trehansiddharth/SignAway/Logs/ADNS-9800 Diagram.png

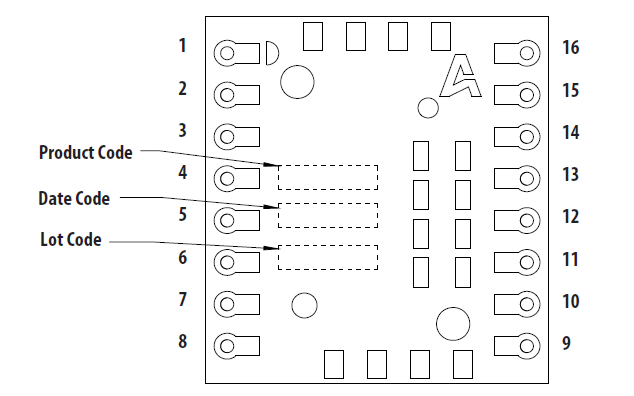
Logs/ADNS-9800 Diagram.png
