trehansiddharth/SignAway/Logs/Low NCS signal on 8051.png

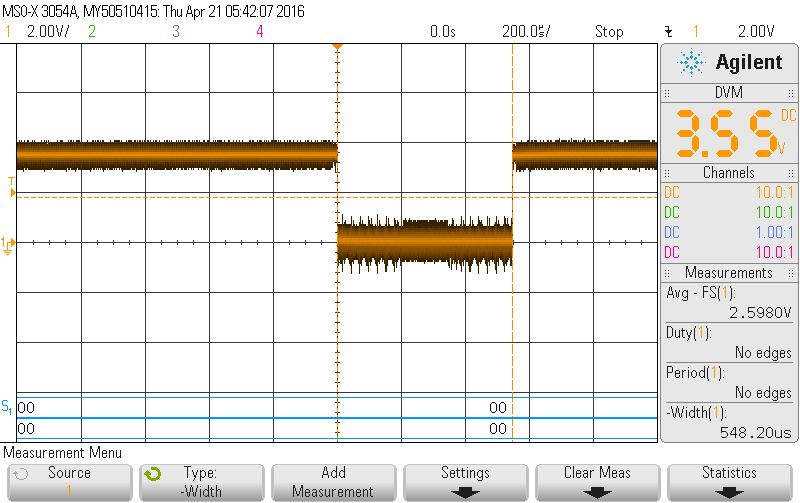
Logs/Low NCS signal on 8051.png
