trehansiddharth/SignAway/Logs/Reading MISO 1.png

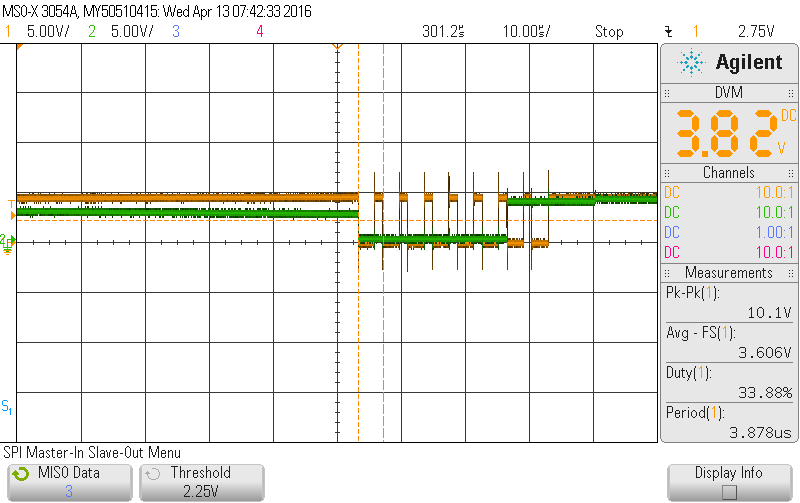
Logs/Reading MISO 1.png
