trehansiddharth/SignAway/Logs/Reading MISO 2.png

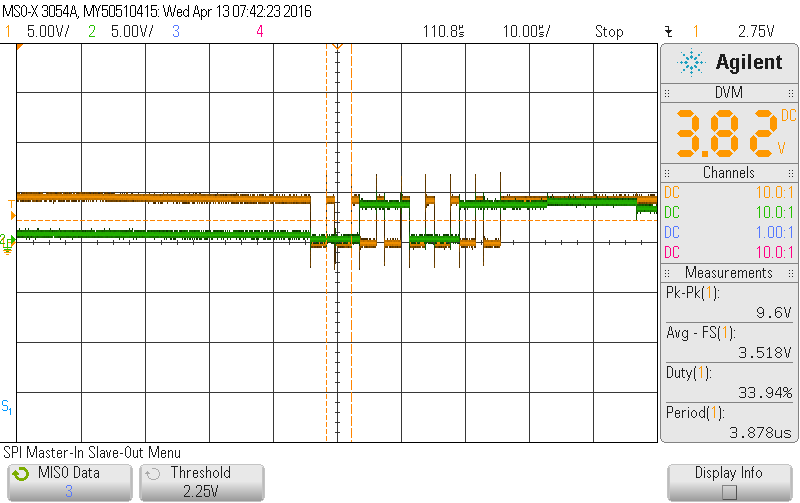
Logs/Reading MISO 2.png
