trehansiddharth/SignAway/Logs/SCLK and MOSI during write on 8051.png

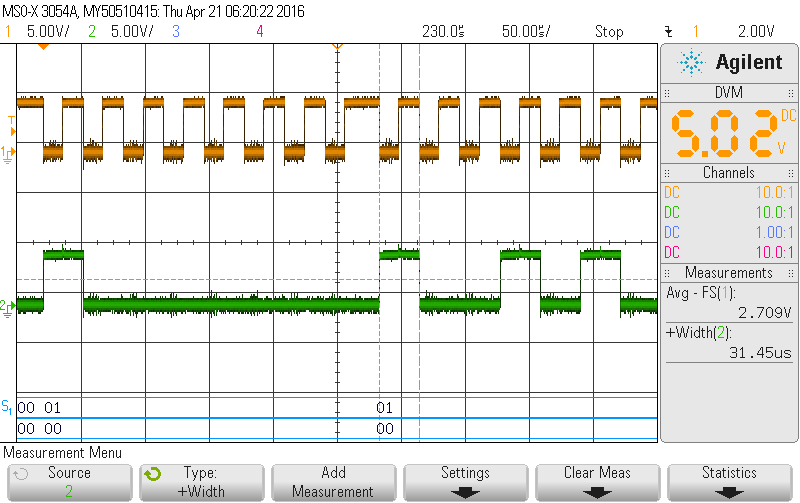
Logs/SCLK and MOSI during write on 8051.png
