trehansiddharth/SignAway/Logs/SCLK during read on 8051.png

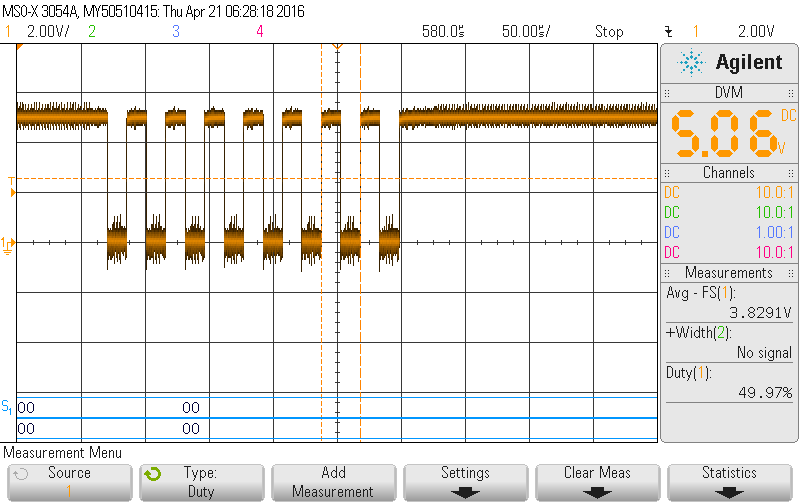
Logs/SCLK during read on 8051.png
