trehansiddharth/SignAway/Logs/SCLK during write on 8051.png

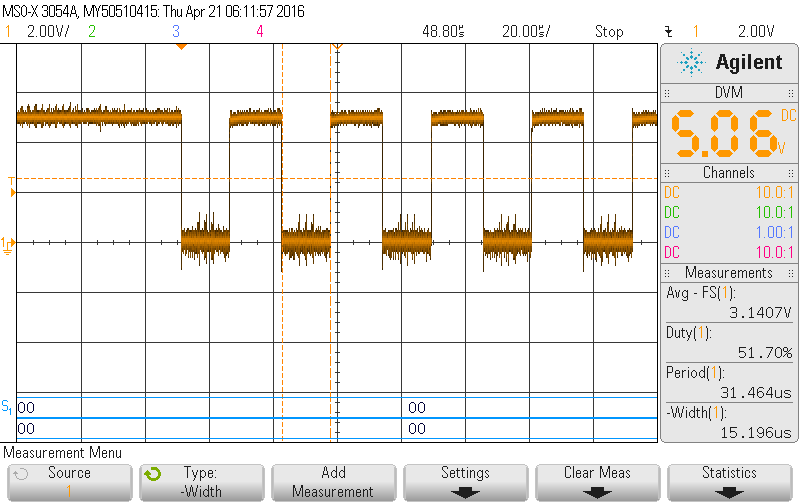
Logs/SCLK during write on 8051.png
