trehansiddharth/SignAway/Logs/Image Burst Operation Timing.png

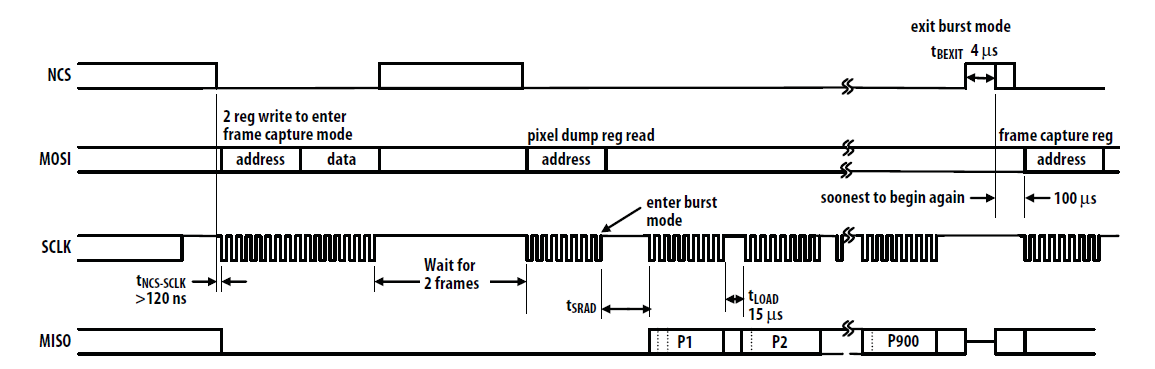
Logs/Image Burst Operation Timing.png
