trehansiddharth/SignAway/Logs/Read Operation Timing.png

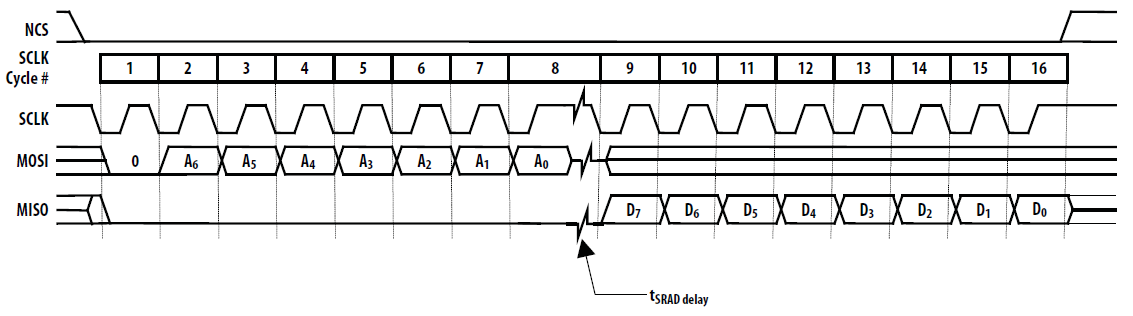
Logs/Read Operation Timing.png
