trehansiddharth/SignAway/Logs/Write Operation Timing.png

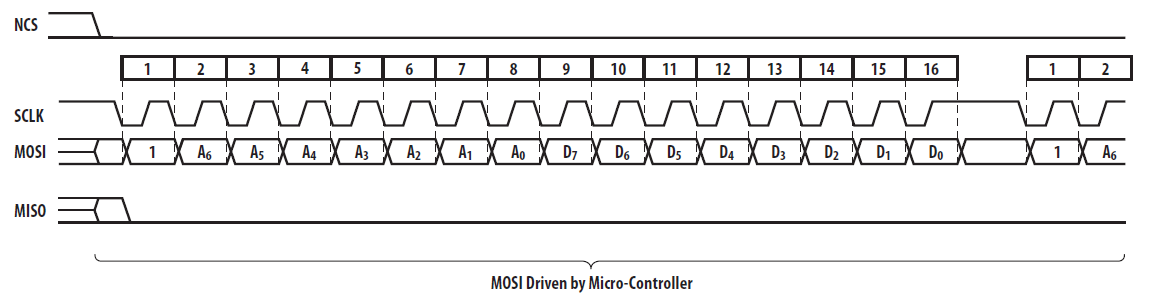
Logs/Write Operation Timing.png
