trehansiddharth/SignAway/Source/PSoC/SignatureVerifier/SignatureVerifier.cydsn/codegentemp/Pin_LED_Green.h

/*******************************************************************************
* File Name: Pin_LED_Green.h  
* Version 2.5
*
* Description:
*  This file containts Control Register function prototypes and register defines
*
* Note:
*
********************************************************************************
* Copyright 2008-2014, Cypress Semiconductor Corporation.  All rights reserved.
* You may use this file only in accordance with the license, terms, conditions, 
* disclaimers, and limitations in the end user license agreement accompanying 
* the software package with which this file was provided.
*******************************************************************************/

#if !defined(CY_PINS_Pin_LED_Green_H) /* Pins Pin_LED_Green_H */
#define CY_PINS_Pin_LED_Green_H

#include "cytypes.h"
#include "cyfitter.h"
#include "Pin_LED_Green_aliases.h"


/***************************************
*        Function Prototypes             
***************************************/    

void    Pin_LED_Green_Write(uint8 value) ;
void    Pin_LED_Green_SetDriveMode(uint8 mode) ;
uint8   Pin_LED_Green_ReadDataReg(void) ;
uint8   Pin_LED_Green_Read(void) ;
uint8   Pin_LED_Green_ClearInterrupt(void) ;


/***************************************
*           API Constants        
***************************************/

/* Drive Modes */
#define Pin_LED_Green_DRIVE_MODE_BITS        (3)
#define Pin_LED_Green_DRIVE_MODE_IND_MASK    (0xFFFFFFFFu >> (32 - Pin_LED_Green_DRIVE_MODE_BITS))
#define Pin_LED_Green_DRIVE_MODE_SHIFT       (0x00u)
#define Pin_LED_Green_DRIVE_MODE_MASK        (0x07u << Pin_LED_Green_DRIVE_MODE_SHIFT)

#define Pin_LED_Green_DM_ALG_HIZ         (0x00u << Pin_LED_Green_DRIVE_MODE_SHIFT)
#define Pin_LED_Green_DM_DIG_HIZ         (0x01u << Pin_LED_Green_DRIVE_MODE_SHIFT)
#define Pin_LED_Green_DM_RES_UP          (0x02u << Pin_LED_Green_DRIVE_MODE_SHIFT)
#define Pin_LED_Green_DM_RES_DWN         (0x03u << Pin_LED_Green_DRIVE_MODE_SHIFT)
#define Pin_LED_Green_DM_OD_LO           (0x04u << Pin_LED_Green_DRIVE_MODE_SHIFT)
#define Pin_LED_Green_DM_OD_HI           (0x05u << Pin_LED_Green_DRIVE_MODE_SHIFT)
#define Pin_LED_Green_DM_STRONG          (0x06u << Pin_LED_Green_DRIVE_MODE_SHIFT)
#define Pin_LED_Green_DM_RES_UPDWN       (0x07u << Pin_LED_Green_DRIVE_MODE_SHIFT)

/* Digital Port Constants */
#define Pin_LED_Green_MASK               Pin_LED_Green__MASK
#define Pin_LED_Green_SHIFT              Pin_LED_Green__SHIFT
#define Pin_LED_Green_WIDTH              1u


/***************************************
*             Registers        
***************************************/

/* Main Port Registers */
/* Pin State */
#define Pin_LED_Green_PS                     (* (reg32 *) Pin_LED_Green__PS)
/* Port Configuration */
#define Pin_LED_Green_PC                     (* (reg32 *) Pin_LED_Green__PC)
/* Data Register */
#define Pin_LED_Green_DR                     (* (reg32 *) Pin_LED_Green__DR)
/* Input Buffer Disable Override */
#define Pin_LED_Green_INP_DIS                (* (reg32 *) Pin_LED_Green__PC2)


#if defined(Pin_LED_Green__INTSTAT)  /* Interrupt Registers */

    #define Pin_LED_Green_INTSTAT                (* (reg32 *) Pin_LED_Green__INTSTAT)

#endif /* Interrupt Registers */

#endif /* End Pins Pin_LED_Green_H */


/* [] END OF FILE */
