trehansiddharth/SignAway/Source/PSoC/SignatureVerifier/SignatureVerifier.cydsn/codegentemp/Pin_SS.h

/*******************************************************************************
* File Name: Pin_SS.h  
* Version 2.5
*
* Description:
*  This file containts Control Register function prototypes and register defines
*
* Note:
*
********************************************************************************
* Copyright 2008-2014, Cypress Semiconductor Corporation.  All rights reserved.
* You may use this file only in accordance with the license, terms, conditions, 
* disclaimers, and limitations in the end user license agreement accompanying 
* the software package with which this file was provided.
*******************************************************************************/

#if !defined(CY_PINS_Pin_SS_H) /* Pins Pin_SS_H */
#define CY_PINS_Pin_SS_H

#include "cytypes.h"
#include "cyfitter.h"
#include "Pin_SS_aliases.h"


/***************************************
*        Function Prototypes             
***************************************/    

void    Pin_SS_Write(uint8 value) ;
void    Pin_SS_SetDriveMode(uint8 mode) ;
uint8   Pin_SS_ReadDataReg(void) ;
uint8   Pin_SS_Read(void) ;
uint8   Pin_SS_ClearInterrupt(void) ;


/***************************************
*           API Constants        
***************************************/

/* Drive Modes */
#define Pin_SS_DRIVE_MODE_BITS        (3)
#define Pin_SS_DRIVE_MODE_IND_MASK    (0xFFFFFFFFu >> (32 - Pin_SS_DRIVE_MODE_BITS))
#define Pin_SS_DRIVE_MODE_SHIFT       (0x00u)
#define Pin_SS_DRIVE_MODE_MASK        (0x07u << Pin_SS_DRIVE_MODE_SHIFT)

#define Pin_SS_DM_ALG_HIZ         (0x00u << Pin_SS_DRIVE_MODE_SHIFT)
#define Pin_SS_DM_DIG_HIZ         (0x01u << Pin_SS_DRIVE_MODE_SHIFT)
#define Pin_SS_DM_RES_UP          (0x02u << Pin_SS_DRIVE_MODE_SHIFT)
#define Pin_SS_DM_RES_DWN         (0x03u << Pin_SS_DRIVE_MODE_SHIFT)
#define Pin_SS_DM_OD_LO           (0x04u << Pin_SS_DRIVE_MODE_SHIFT)
#define Pin_SS_DM_OD_HI           (0x05u << Pin_SS_DRIVE_MODE_SHIFT)
#define Pin_SS_DM_STRONG          (0x06u << Pin_SS_DRIVE_MODE_SHIFT)
#define Pin_SS_DM_RES_UPDWN       (0x07u << Pin_SS_DRIVE_MODE_SHIFT)

/* Digital Port Constants */
#define Pin_SS_MASK               Pin_SS__MASK
#define Pin_SS_SHIFT              Pin_SS__SHIFT
#define Pin_SS_WIDTH              1u


/***************************************
*             Registers        
***************************************/

/* Main Port Registers */
/* Pin State */
#define Pin_SS_PS                     (* (reg32 *) Pin_SS__PS)
/* Port Configuration */
#define Pin_SS_PC                     (* (reg32 *) Pin_SS__PC)
/* Data Register */
#define Pin_SS_DR                     (* (reg32 *) Pin_SS__DR)
/* Input Buffer Disable Override */
#define Pin_SS_INP_DIS                (* (reg32 *) Pin_SS__PC2)


#if defined(Pin_SS__INTSTAT)  /* Interrupt Registers */

    #define Pin_SS_INTSTAT                (* (reg32 *) Pin_SS__INTSTAT)

#endif /* Interrupt Registers */

#endif /* End Pins Pin_SS_H */


/* [] END OF FILE */
