trehansiddharth/SignAway/Source/PSoC/SignatureVerifier/SignatureVerifier.cydsn/codegentemp/cyfitter.h

#ifndef INCLUDED_CYFITTER_H
#define INCLUDED_CYFITTER_H
#include <cydevice_trm.h>

/* SPI_BSPIS */
#define SPI_BSPIS_es3_SPISlave_BitCounter__16BIT_CONTROL_AUX_CTL_REG CYREG_UDB_W16_ACTL_02
#define SPI_BSPIS_es3_SPISlave_BitCounter__16BIT_CONTROL_CONTROL_REG CYREG_UDB_W16_CTL_02
#define SPI_BSPIS_es3_SPISlave_BitCounter__16BIT_CONTROL_COUNT_REG CYREG_UDB_W16_CTL_02
#define SPI_BSPIS_es3_SPISlave_BitCounter__16BIT_COUNT_CONTROL_REG CYREG_UDB_W16_CTL_02
#define SPI_BSPIS_es3_SPISlave_BitCounter__16BIT_COUNT_COUNT_REG CYREG_UDB_W16_CTL_02
#define SPI_BSPIS_es3_SPISlave_BitCounter__16BIT_MASK_MASK_REG CYREG_UDB_W16_MSK_02
#define SPI_BSPIS_es3_SPISlave_BitCounter__16BIT_MASK_PERIOD_REG CYREG_UDB_W16_MSK_02
#define SPI_BSPIS_es3_SPISlave_BitCounter__16BIT_PERIOD_MASK_REG CYREG_UDB_W16_MSK_02
#define SPI_BSPIS_es3_SPISlave_BitCounter__16BIT_PERIOD_PERIOD_REG CYREG_UDB_W16_MSK_02
#define SPI_BSPIS_es3_SPISlave_BitCounter__CONTROL_AUX_CTL_REG CYREG_UDB_W8_ACTL_02
#define SPI_BSPIS_es3_SPISlave_BitCounter__CONTROL_REG CYREG_UDB_W8_CTL_02
#define SPI_BSPIS_es3_SPISlave_BitCounter__CONTROL_ST_REG CYREG_UDB_CAT16_CTL_ST_02
#define SPI_BSPIS_es3_SPISlave_BitCounter__COUNT_REG CYREG_UDB_W8_CTL_02
#define SPI_BSPIS_es3_SPISlave_BitCounter__COUNT_ST_REG CYREG_UDB_CAT16_CTL_ST_02
#define SPI_BSPIS_es3_SPISlave_BitCounter__MASK_CTL_AUX_CTL_REG CYREG_UDB_CAT16_ACTL_MSK_02
#define SPI_BSPIS_es3_SPISlave_BitCounter__PER_CTL_AUX_CTL_REG CYREG_UDB_CAT16_ACTL_MSK_02
#define SPI_BSPIS_es3_SPISlave_BitCounter__PERIOD_REG CYREG_UDB_W8_MSK_02
#define SPI_BSPIS_es3_SPISlave_BitCounter_ST__16BIT_STATUS_AUX_CTL_REG CYREG_UDB_W16_ACTL_02
#define SPI_BSPIS_es3_SPISlave_BitCounter_ST__16BIT_STATUS_REG CYREG_UDB_W16_ST_02
#define SPI_BSPIS_es3_SPISlave_BitCounter_ST__MASK_REG CYREG_UDB_W8_MSK_02
#define SPI_BSPIS_es3_SPISlave_BitCounter_ST__MASK_ST_AUX_CTL_REG CYREG_UDB_CAT16_ACTL_MSK_02
#define SPI_BSPIS_es3_SPISlave_BitCounter_ST__PER_ST_AUX_CTL_REG CYREG_UDB_CAT16_ACTL_MSK_02
#define SPI_BSPIS_es3_SPISlave_BitCounter_ST__STATUS_AUX_CTL_REG CYREG_UDB_W8_ACTL_02
#define SPI_BSPIS_es3_SPISlave_BitCounter_ST__STATUS_CNT_REG CYREG_UDB_CAT16_CTL_ST_02
#define SPI_BSPIS_es3_SPISlave_BitCounter_ST__STATUS_CONTROL_REG CYREG_UDB_CAT16_CTL_ST_02
#define SPI_BSPIS_es3_SPISlave_BitCounter_ST__STATUS_REG CYREG_UDB_W8_ST_02
#define SPI_BSPIS_es3_SPISlave_RxStsReg__16BIT_STATUS_AUX_CTL_REG CYREG_UDB_W16_ACTL_01
#define SPI_BSPIS_es3_SPISlave_RxStsReg__16BIT_STATUS_REG CYREG_UDB_W16_ST_01
#define SPI_BSPIS_es3_SPISlave_RxStsReg__3__MASK 0x08u
#define SPI_BSPIS_es3_SPISlave_RxStsReg__3__POS 3
#define SPI_BSPIS_es3_SPISlave_RxStsReg__4__MASK 0x10u
#define SPI_BSPIS_es3_SPISlave_RxStsReg__4__POS 4
#define SPI_BSPIS_es3_SPISlave_RxStsReg__5__MASK 0x20u
#define SPI_BSPIS_es3_SPISlave_RxStsReg__5__POS 5
#define SPI_BSPIS_es3_SPISlave_RxStsReg__6__MASK 0x40u
#define SPI_BSPIS_es3_SPISlave_RxStsReg__6__POS 6
#define SPI_BSPIS_es3_SPISlave_RxStsReg__MASK 0x78u
#define SPI_BSPIS_es3_SPISlave_RxStsReg__MASK_REG CYREG_UDB_W8_MSK_01
#define SPI_BSPIS_es3_SPISlave_RxStsReg__STATUS_AUX_CTL_REG CYREG_UDB_W8_ACTL_01
#define SPI_BSPIS_es3_SPISlave_RxStsReg__STATUS_REG CYREG_UDB_W8_ST_01
#define SPI_BSPIS_es3_SPISlave_sR16_Dp_u0__16BIT_A0_REG CYREG_UDB_W16_A0_02
#define SPI_BSPIS_es3_SPISlave_sR16_Dp_u0__16BIT_A1_REG CYREG_UDB_W16_A1_02
#define SPI_BSPIS_es3_SPISlave_sR16_Dp_u0__16BIT_D0_REG CYREG_UDB_W16_D0_02
#define SPI_BSPIS_es3_SPISlave_sR16_Dp_u0__16BIT_D1_REG CYREG_UDB_W16_D1_02
#define SPI_BSPIS_es3_SPISlave_sR16_Dp_u0__16BIT_DP_AUX_CTL_REG CYREG_UDB_W16_ACTL_02
#define SPI_BSPIS_es3_SPISlave_sR16_Dp_u0__16BIT_F0_REG CYREG_UDB_W16_F0_02
#define SPI_BSPIS_es3_SPISlave_sR16_Dp_u0__16BIT_F1_REG CYREG_UDB_W16_F1_02
#define SPI_BSPIS_es3_SPISlave_sR16_Dp_u0__A0_A1_REG CYREG_UDB_CAT16_A_02
#define SPI_BSPIS_es3_SPISlave_sR16_Dp_u0__A0_REG CYREG_UDB_W8_A0_02
#define SPI_BSPIS_es3_SPISlave_sR16_Dp_u0__A1_REG CYREG_UDB_W8_A1_02
#define SPI_BSPIS_es3_SPISlave_sR16_Dp_u0__D0_D1_REG CYREG_UDB_CAT16_D_02
#define SPI_BSPIS_es3_SPISlave_sR16_Dp_u0__D0_REG CYREG_UDB_W8_D0_02
#define SPI_BSPIS_es3_SPISlave_sR16_Dp_u0__D1_REG CYREG_UDB_W8_D1_02
#define SPI_BSPIS_es3_SPISlave_sR16_Dp_u0__DP_AUX_CTL_REG CYREG_UDB_W8_ACTL_02
#define SPI_BSPIS_es3_SPISlave_sR16_Dp_u0__F0_F1_REG CYREG_UDB_CAT16_F_02
#define SPI_BSPIS_es3_SPISlave_sR16_Dp_u0__F0_REG CYREG_UDB_W8_F0_02
#define SPI_BSPIS_es3_SPISlave_sR16_Dp_u0__F1_REG CYREG_UDB_W8_F1_02
#define SPI_BSPIS_es3_SPISlave_sR16_Dp_u0__MSK_DP_AUX_CTL_REG CYREG_UDB_CAT16_ACTL_MSK_02
#define SPI_BSPIS_es3_SPISlave_sR16_Dp_u0__PER_DP_AUX_CTL_REG CYREG_UDB_CAT16_ACTL_MSK_02
#define SPI_BSPIS_es3_SPISlave_sR16_Dp_u1__A0_A1_REG CYREG_UDB_CAT16_A_03
#define SPI_BSPIS_es3_SPISlave_sR16_Dp_u1__A0_REG CYREG_UDB_W8_A0_03
#define SPI_BSPIS_es3_SPISlave_sR16_Dp_u1__A1_REG CYREG_UDB_W8_A1_03
#define SPI_BSPIS_es3_SPISlave_sR16_Dp_u1__D0_D1_REG CYREG_UDB_CAT16_D_03
#define SPI_BSPIS_es3_SPISlave_sR16_Dp_u1__D0_REG CYREG_UDB_W8_D0_03
#define SPI_BSPIS_es3_SPISlave_sR16_Dp_u1__D1_REG CYREG_UDB_W8_D1_03
#define SPI_BSPIS_es3_SPISlave_sR16_Dp_u1__DP_AUX_CTL_REG CYREG_UDB_W8_ACTL_03
#define SPI_BSPIS_es3_SPISlave_sR16_Dp_u1__F0_F1_REG CYREG_UDB_CAT16_F_03
#define SPI_BSPIS_es3_SPISlave_sR16_Dp_u1__F0_REG CYREG_UDB_W8_F0_03
#define SPI_BSPIS_es3_SPISlave_sR16_Dp_u1__F1_REG CYREG_UDB_W8_F1_03
#define SPI_BSPIS_es3_SPISlave_TxStsReg__0__MASK 0x01u
#define SPI_BSPIS_es3_SPISlave_TxStsReg__0__POS 0
#define SPI_BSPIS_es3_SPISlave_TxStsReg__1__MASK 0x02u
#define SPI_BSPIS_es3_SPISlave_TxStsReg__1__POS 1
#define SPI_BSPIS_es3_SPISlave_TxStsReg__2__MASK 0x04u
#define SPI_BSPIS_es3_SPISlave_TxStsReg__2__POS 2
#define SPI_BSPIS_es3_SPISlave_TxStsReg__6__MASK 0x40u
#define SPI_BSPIS_es3_SPISlave_TxStsReg__6__POS 6
#define SPI_BSPIS_es3_SPISlave_TxStsReg__MASK 0x47u
#define SPI_BSPIS_es3_SPISlave_TxStsReg__MASK_REG CYREG_UDB_W8_MSK_03
#define SPI_BSPIS_es3_SPISlave_TxStsReg__STATUS_AUX_CTL_REG CYREG_UDB_W8_ACTL_03
#define SPI_BSPIS_es3_SPISlave_TxStsReg__STATUS_REG CYREG_UDB_W8_ST_03

/* SPI_Clock */
#define SPI_Clock__DIVIDER_MASK 0x0000FFFFu
#define SPI_Clock__ENABLE CYREG_CLK_DIVIDER_A00
#define SPI_Clock__ENABLE_MASK 0x80000000u
#define SPI_Clock__MASK 0x80000000u
#define SPI_Clock__REGISTER CYREG_CLK_DIVIDER_A00

/* SPI_RxInternalInterrupt */
#define SPI_RxInternalInterrupt__INTC_CLR_EN_REG CYREG_CM0_ICER
#define SPI_RxInternalInterrupt__INTC_CLR_PD_REG CYREG_CM0_ICPR
#define SPI_RxInternalInterrupt__INTC_MASK 0x01u
#define SPI_RxInternalInterrupt__INTC_NUMBER 0u
#define SPI_RxInternalInterrupt__INTC_PRIOR_MASK 0xC0u
#define SPI_RxInternalInterrupt__INTC_PRIOR_NUM 3u
#define SPI_RxInternalInterrupt__INTC_PRIOR_REG CYREG_CM0_IPR0
#define SPI_RxInternalInterrupt__INTC_SET_EN_REG CYREG_CM0_ISER
#define SPI_RxInternalInterrupt__INTC_SET_PD_REG CYREG_CM0_ISPR

/* UART_rx */
#define UART_rx__0__DM__MASK 0x07u
#define UART_rx__0__DM__SHIFT 0
#define UART_rx__0__DR CYREG_PRT3_DR
#define UART_rx__0__HSIOM CYREG_HSIOM_PORT_SEL3
#define UART_rx__0__HSIOM_MASK 0x0000000Fu
#define UART_rx__0__HSIOM_SHIFT 0u
#define UART_rx__0__INTCFG CYREG_PRT3_INTCFG
#define UART_rx__0__INTSTAT CYREG_PRT3_INTSTAT
#define UART_rx__0__MASK 0x01u
#define UART_rx__0__PA__CFG0 CYREG_UDB_PA3_CFG0
#define UART_rx__0__PA__CFG1 CYREG_UDB_PA3_CFG1
#define UART_rx__0__PA__CFG10 CYREG_UDB_PA3_CFG10
#define UART_rx__0__PA__CFG11 CYREG_UDB_PA3_CFG11
#define UART_rx__0__PA__CFG12 CYREG_UDB_PA3_CFG12
#define UART_rx__0__PA__CFG13 CYREG_UDB_PA3_CFG13
#define UART_rx__0__PA__CFG14 CYREG_UDB_PA3_CFG14
#define UART_rx__0__PA__CFG2 CYREG_UDB_PA3_CFG2
#define UART_rx__0__PA__CFG3 CYREG_UDB_PA3_CFG3
#define UART_rx__0__PA__CFG4 CYREG_UDB_PA3_CFG4
#define UART_rx__0__PA__CFG5 CYREG_UDB_PA3_CFG5
#define UART_rx__0__PA__CFG6 CYREG_UDB_PA3_CFG6
#define UART_rx__0__PA__CFG7 CYREG_UDB_PA3_CFG7
#define UART_rx__0__PA__CFG8 CYREG_UDB_PA3_CFG8
#define UART_rx__0__PA__CFG9 CYREG_UDB_PA3_CFG9
#define UART_rx__0__PC CYREG_PRT3_PC
#define UART_rx__0__PC2 CYREG_PRT3_PC2
#define UART_rx__0__PORT 3u
#define UART_rx__0__PS CYREG_PRT3_PS
#define UART_rx__0__SHIFT 0
#define UART_rx__DR CYREG_PRT3_DR
#define UART_rx__INTCFG CYREG_PRT3_INTCFG
#define UART_rx__INTSTAT CYREG_PRT3_INTSTAT
#define UART_rx__MASK 0x01u
#define UART_rx__PA__CFG0 CYREG_UDB_PA3_CFG0
#define UART_rx__PA__CFG1 CYREG_UDB_PA3_CFG1
#define UART_rx__PA__CFG10 CYREG_UDB_PA3_CFG10
#define UART_rx__PA__CFG11 CYREG_UDB_PA3_CFG11
#define UART_rx__PA__CFG12 CYREG_UDB_PA3_CFG12
#define UART_rx__PA__CFG13 CYREG_UDB_PA3_CFG13
#define UART_rx__PA__CFG14 CYREG_UDB_PA3_CFG14
#define UART_rx__PA__CFG2 CYREG_UDB_PA3_CFG2
#define UART_rx__PA__CFG3 CYREG_UDB_PA3_CFG3
#define UART_rx__PA__CFG4 CYREG_UDB_PA3_CFG4
#define UART_rx__PA__CFG5 CYREG_UDB_PA3_CFG5
#define UART_rx__PA__CFG6 CYREG_UDB_PA3_CFG6
#define UART_rx__PA__CFG7 CYREG_UDB_PA3_CFG7
#define UART_rx__PA__CFG8 CYREG_UDB_PA3_CFG8
#define UART_rx__PA__CFG9 CYREG_UDB_PA3_CFG9
#define UART_rx__PC CYREG_PRT3_PC
#define UART_rx__PC2 CYREG_PRT3_PC2
#define UART_rx__PORT 3u
#define UART_rx__PS CYREG_PRT3_PS
#define UART_rx__SHIFT 0

/* UART_SCB */
#define UART_SCB__BIST_CONTROL CYREG_SCB1_BIST_CONTROL
#define UART_SCB__BIST_DATA CYREG_SCB1_BIST_DATA
#define UART_SCB__CTRL CYREG_SCB1_CTRL
#define UART_SCB__EZ_DATA00 CYREG_SCB1_EZ_DATA00
#define UART_SCB__EZ_DATA01 CYREG_SCB1_EZ_DATA01
#define UART_SCB__EZ_DATA02 CYREG_SCB1_EZ_DATA02
#define UART_SCB__EZ_DATA03 CYREG_SCB1_EZ_DATA03
#define UART_SCB__EZ_DATA04 CYREG_SCB1_EZ_DATA04
#define UART_SCB__EZ_DATA05 CYREG_SCB1_EZ_DATA05
#define UART_SCB__EZ_DATA06 CYREG_SCB1_EZ_DATA06
#define UART_SCB__EZ_DATA07 CYREG_SCB1_EZ_DATA07
#define UART_SCB__EZ_DATA08 CYREG_SCB1_EZ_DATA08
#define UART_SCB__EZ_DATA09 CYREG_SCB1_EZ_DATA09
#define UART_SCB__EZ_DATA10 CYREG_SCB1_EZ_DATA10
#define UART_SCB__EZ_DATA11 CYREG_SCB1_EZ_DATA11
#define UART_SCB__EZ_DATA12 CYREG_SCB1_EZ_DATA12
#define UART_SCB__EZ_DATA13 CYREG_SCB1_EZ_DATA13
#define UART_SCB__EZ_DATA14 CYREG_SCB1_EZ_DATA14
#define UART_SCB__EZ_DATA15 CYREG_SCB1_EZ_DATA15
#define UART_SCB__EZ_DATA16 CYREG_SCB1_EZ_DATA16
#define UART_SCB__EZ_DATA17 CYREG_SCB1_EZ_DATA17
#define UART_SCB__EZ_DATA18 CYREG_SCB1_EZ_DATA18
#define UART_SCB__EZ_DATA19 CYREG_SCB1_EZ_DATA19
#define UART_SCB__EZ_DATA20 CYREG_SCB1_EZ_DATA20
#define UART_SCB__EZ_DATA21 CYREG_SCB1_EZ_DATA21
#define UART_SCB__EZ_DATA22 CYREG_SCB1_EZ_DATA22
#define UART_SCB__EZ_DATA23 CYREG_SCB1_EZ_DATA23
#define UART_SCB__EZ_DATA24 CYREG_SCB1_EZ_DATA24
#define UART_SCB__EZ_DATA25 CYREG_SCB1_EZ_DATA25
#define UART_SCB__EZ_DATA26 CYREG_SCB1_EZ_DATA26
#define UART_SCB__EZ_DATA27 CYREG_SCB1_EZ_DATA27
#define UART_SCB__EZ_DATA28 CYREG_SCB1_EZ_DATA28
#define UART_SCB__EZ_DATA29 CYREG_SCB1_EZ_DATA29
#define UART_SCB__EZ_DATA30 CYREG_SCB1_EZ_DATA30
#define UART_SCB__EZ_DATA31 CYREG_SCB1_EZ_DATA31
#define UART_SCB__I2C_CFG CYREG_SCB1_I2C_CFG
#define UART_SCB__I2C_CTRL CYREG_SCB1_I2C_CTRL
#define UART_SCB__I2C_M_CMD CYREG_SCB1_I2C_M_CMD
#define UART_SCB__I2C_S_CMD CYREG_SCB1_I2C_S_CMD
#define UART_SCB__I2C_STATUS CYREG_SCB1_I2C_STATUS
#define UART_SCB__INTR_CAUSE CYREG_SCB1_INTR_CAUSE
#define UART_SCB__INTR_I2C_EC CYREG_SCB1_INTR_I2C_EC
#define UART_SCB__INTR_I2C_EC_MASK CYREG_SCB1_INTR_I2C_EC_MASK
#define UART_SCB__INTR_I2C_EC_MASKED CYREG_SCB1_INTR_I2C_EC_MASKED
#define UART_SCB__INTR_M CYREG_SCB1_INTR_M
#define UART_SCB__INTR_M_MASK CYREG_SCB1_INTR_M_MASK
#define UART_SCB__INTR_M_MASKED CYREG_SCB1_INTR_M_MASKED
#define UART_SCB__INTR_M_SET CYREG_SCB1_INTR_M_SET
#define UART_SCB__INTR_RX CYREG_SCB1_INTR_RX
#define UART_SCB__INTR_RX_MASK CYREG_SCB1_INTR_RX_MASK
#define UART_SCB__INTR_RX_MASKED CYREG_SCB1_INTR_RX_MASKED
#define UART_SCB__INTR_RX_SET CYREG_SCB1_INTR_RX_SET
#define UART_SCB__INTR_S CYREG_SCB1_INTR_S
#define UART_SCB__INTR_S_MASK CYREG_SCB1_INTR_S_MASK
#define UART_SCB__INTR_S_MASKED CYREG_SCB1_INTR_S_MASKED
#define UART_SCB__INTR_S_SET CYREG_SCB1_INTR_S_SET
#define UART_SCB__INTR_SPI_EC CYREG_SCB1_INTR_SPI_EC
#define UART_SCB__INTR_SPI_EC_MASK CYREG_SCB1_INTR_SPI_EC_MASK
#define UART_SCB__INTR_SPI_EC_MASKED CYREG_SCB1_INTR_SPI_EC_MASKED
#define UART_SCB__INTR_TX CYREG_SCB1_INTR_TX
#define UART_SCB__INTR_TX_MASK CYREG_SCB1_INTR_TX_MASK
#define UART_SCB__INTR_TX_MASKED CYREG_SCB1_INTR_TX_MASKED
#define UART_SCB__INTR_TX_SET CYREG_SCB1_INTR_TX_SET
#define UART_SCB__RX_CTRL CYREG_SCB1_RX_CTRL
#define UART_SCB__RX_FIFO_CTRL CYREG_SCB1_RX_FIFO_CTRL
#define UART_SCB__RX_FIFO_RD CYREG_SCB1_RX_FIFO_RD
#define UART_SCB__RX_FIFO_RD_SILENT CYREG_SCB1_RX_FIFO_RD_SILENT
#define UART_SCB__RX_FIFO_STATUS CYREG_SCB1_RX_FIFO_STATUS
#define UART_SCB__RX_MATCH CYREG_SCB1_RX_MATCH
#define UART_SCB__SPI_CTRL CYREG_SCB1_SPI_CTRL
#define UART_SCB__SPI_STATUS CYREG_SCB1_SPI_STATUS
#define UART_SCB__STATUS CYREG_SCB1_STATUS
#define UART_SCB__TX_CTRL CYREG_SCB1_TX_CTRL
#define UART_SCB__TX_FIFO_CTRL CYREG_SCB1_TX_FIFO_CTRL
#define UART_SCB__TX_FIFO_STATUS CYREG_SCB1_TX_FIFO_STATUS
#define UART_SCB__TX_FIFO_WR CYREG_SCB1_TX_FIFO_WR
#define UART_SCB__UART_CTRL CYREG_SCB1_UART_CTRL
#define UART_SCB__UART_RX_CTRL CYREG_SCB1_UART_RX_CTRL
#define UART_SCB__UART_RX_STATUS CYREG_SCB1_UART_RX_STATUS
#define UART_SCB__UART_TX_CTRL CYREG_SCB1_UART_TX_CTRL

/* UART_SCBCLK */
#define UART_SCBCLK__DIVIDER_MASK 0x0000FFFFu
#define UART_SCBCLK__ENABLE CYREG_CLK_DIVIDER_B00
#define UART_SCBCLK__ENABLE_MASK 0x80000000u
#define UART_SCBCLK__MASK 0x80000000u
#define UART_SCBCLK__REGISTER CYREG_CLK_DIVIDER_B00

/* UART_tx */
#define UART_tx__0__DM__MASK 0x38u
#define UART_tx__0__DM__SHIFT 3
#define UART_tx__0__DR CYREG_PRT3_DR
#define UART_tx__0__HSIOM CYREG_HSIOM_PORT_SEL3
#define UART_tx__0__HSIOM_MASK 0x000000F0u
#define UART_tx__0__HSIOM_SHIFT 4u
#define UART_tx__0__INTCFG CYREG_PRT3_INTCFG
#define UART_tx__0__INTSTAT CYREG_PRT3_INTSTAT
#define UART_tx__0__MASK 0x02u
#define UART_tx__0__OUT_SEL CYREG_UDB_PA3_CFG10
#define UART_tx__0__OUT_SEL_SHIFT 2u
#define UART_tx__0__OUT_SEL_VAL -1u
#define UART_tx__0__PA__CFG0 CYREG_UDB_PA3_CFG0
#define UART_tx__0__PA__CFG1 CYREG_UDB_PA3_CFG1
#define UART_tx__0__PA__CFG10 CYREG_UDB_PA3_CFG10
#define UART_tx__0__PA__CFG11 CYREG_UDB_PA3_CFG11
#define UART_tx__0__PA__CFG12 CYREG_UDB_PA3_CFG12
#define UART_tx__0__PA__CFG13 CYREG_UDB_PA3_CFG13
#define UART_tx__0__PA__CFG14 CYREG_UDB_PA3_CFG14
#define UART_tx__0__PA__CFG2 CYREG_UDB_PA3_CFG2
#define UART_tx__0__PA__CFG3 CYREG_UDB_PA3_CFG3
#define UART_tx__0__PA__CFG4 CYREG_UDB_PA3_CFG4
#define UART_tx__0__PA__CFG5 CYREG_UDB_PA3_CFG5
#define UART_tx__0__PA__CFG6 CYREG_UDB_PA3_CFG6
#define UART_tx__0__PA__CFG7 CYREG_UDB_PA3_CFG7
#define UART_tx__0__PA__CFG8 CYREG_UDB_PA3_CFG8
#define UART_tx__0__PA__CFG9 CYREG_UDB_PA3_CFG9
#define UART_tx__0__PC CYREG_PRT3_PC
#define UART_tx__0__PC2 CYREG_PRT3_PC2
#define UART_tx__0__PORT 3u
#define UART_tx__0__PS CYREG_PRT3_PS
#define UART_tx__0__SHIFT 1
#define UART_tx__DR CYREG_PRT3_DR
#define UART_tx__INTCFG CYREG_PRT3_INTCFG
#define UART_tx__INTSTAT CYREG_PRT3_INTSTAT
#define UART_tx__MASK 0x02u
#define UART_tx__PA__CFG0 CYREG_UDB_PA3_CFG0
#define UART_tx__PA__CFG1 CYREG_UDB_PA3_CFG1
#define UART_tx__PA__CFG10 CYREG_UDB_PA3_CFG10
#define UART_tx__PA__CFG11 CYREG_UDB_PA3_CFG11
#define UART_tx__PA__CFG12 CYREG_UDB_PA3_CFG12
#define UART_tx__PA__CFG13 CYREG_UDB_PA3_CFG13
#define UART_tx__PA__CFG14 CYREG_UDB_PA3_CFG14
#define UART_tx__PA__CFG2 CYREG_UDB_PA3_CFG2
#define UART_tx__PA__CFG3 CYREG_UDB_PA3_CFG3
#define UART_tx__PA__CFG4 CYREG_UDB_PA3_CFG4
#define UART_tx__PA__CFG5 CYREG_UDB_PA3_CFG5
#define UART_tx__PA__CFG6 CYREG_UDB_PA3_CFG6
#define UART_tx__PA__CFG7 CYREG_UDB_PA3_CFG7
#define UART_tx__PA__CFG8 CYREG_UDB_PA3_CFG8
#define UART_tx__PA__CFG9 CYREG_UDB_PA3_CFG9
#define UART_tx__PC CYREG_PRT3_PC
#define UART_tx__PC2 CYREG_PRT3_PC2
#define UART_tx__PORT 3u
#define UART_tx__PS CYREG_PRT3_PS
#define UART_tx__SHIFT 1

/* Pin_SS */
#define Pin_SS__0__DM__MASK 0x1C0u
#define Pin_SS__0__DM__SHIFT 6
#define Pin_SS__0__DR CYREG_PRT0_DR
#define Pin_SS__0__HSIOM CYREG_HSIOM_PORT_SEL0
#define Pin_SS__0__HSIOM_MASK 0x00000F00u
#define Pin_SS__0__HSIOM_SHIFT 8u
#define Pin_SS__0__INTCFG CYREG_PRT0_INTCFG
#define Pin_SS__0__INTSTAT CYREG_PRT0_INTSTAT
#define Pin_SS__0__MASK 0x04u
#define Pin_SS__0__PA__CFG0 CYREG_UDB_PA0_CFG0
#define Pin_SS__0__PA__CFG1 CYREG_UDB_PA0_CFG1
#define Pin_SS__0__PA__CFG10 CYREG_UDB_PA0_CFG10
#define Pin_SS__0__PA__CFG11 CYREG_UDB_PA0_CFG11
#define Pin_SS__0__PA__CFG12 CYREG_UDB_PA0_CFG12
#define Pin_SS__0__PA__CFG13 CYREG_UDB_PA0_CFG13
#define Pin_SS__0__PA__CFG14 CYREG_UDB_PA0_CFG14
#define Pin_SS__0__PA__CFG2 CYREG_UDB_PA0_CFG2
#define Pin_SS__0__PA__CFG3 CYREG_UDB_PA0_CFG3
#define Pin_SS__0__PA__CFG4 CYREG_UDB_PA0_CFG4
#define Pin_SS__0__PA__CFG5 CYREG_UDB_PA0_CFG5
#define Pin_SS__0__PA__CFG6 CYREG_UDB_PA0_CFG6
#define Pin_SS__0__PA__CFG7 CYREG_UDB_PA0_CFG7
#define Pin_SS__0__PA__CFG8 CYREG_UDB_PA0_CFG8
#define Pin_SS__0__PA__CFG9 CYREG_UDB_PA0_CFG9
#define Pin_SS__0__PC CYREG_PRT0_PC
#define Pin_SS__0__PC2 CYREG_PRT0_PC2
#define Pin_SS__0__PORT 0u
#define Pin_SS__0__PS CYREG_PRT0_PS
#define Pin_SS__0__SHIFT 2
#define Pin_SS__DR CYREG_PRT0_DR
#define Pin_SS__INTCFG CYREG_PRT0_INTCFG
#define Pin_SS__INTSTAT CYREG_PRT0_INTSTAT
#define Pin_SS__MASK 0x04u
#define Pin_SS__PA__CFG0 CYREG_UDB_PA0_CFG0
#define Pin_SS__PA__CFG1 CYREG_UDB_PA0_CFG1
#define Pin_SS__PA__CFG10 CYREG_UDB_PA0_CFG10
#define Pin_SS__PA__CFG11 CYREG_UDB_PA0_CFG11
#define Pin_SS__PA__CFG12 CYREG_UDB_PA0_CFG12
#define Pin_SS__PA__CFG13 CYREG_UDB_PA0_CFG13
#define Pin_SS__PA__CFG14 CYREG_UDB_PA0_CFG14
#define Pin_SS__PA__CFG2 CYREG_UDB_PA0_CFG2
#define Pin_SS__PA__CFG3 CYREG_UDB_PA0_CFG3
#define Pin_SS__PA__CFG4 CYREG_UDB_PA0_CFG4
#define Pin_SS__PA__CFG5 CYREG_UDB_PA0_CFG5
#define Pin_SS__PA__CFG6 CYREG_UDB_PA0_CFG6
#define Pin_SS__PA__CFG7 CYREG_UDB_PA0_CFG7
#define Pin_SS__PA__CFG8 CYREG_UDB_PA0_CFG8
#define Pin_SS__PA__CFG9 CYREG_UDB_PA0_CFG9
#define Pin_SS__PC CYREG_PRT0_PC
#define Pin_SS__PC2 CYREG_PRT0_PC2
#define Pin_SS__PORT 0u
#define Pin_SS__PS CYREG_PRT0_PS
#define Pin_SS__SHIFT 2

/* isr_spi */
#define isr_spi__INTC_CLR_EN_REG CYREG_CM0_ICER
#define isr_spi__INTC_CLR_PD_REG CYREG_CM0_ICPR
#define isr_spi__INTC_MASK 0x02u
#define isr_spi__INTC_NUMBER 1u
#define isr_spi__INTC_PRIOR_MASK 0xC000u
#define isr_spi__INTC_PRIOR_NUM 3u
#define isr_spi__INTC_PRIOR_REG CYREG_CM0_IPR0
#define isr_spi__INTC_SET_EN_REG CYREG_CM0_ISER
#define isr_spi__INTC_SET_PD_REG CYREG_CM0_ISPR

/* Pin_MOSI */
#define Pin_MOSI__0__DM__MASK 0x07u
#define Pin_MOSI__0__DM__SHIFT 0
#define Pin_MOSI__0__DR CYREG_PRT0_DR
#define Pin_MOSI__0__HSIOM CYREG_HSIOM_PORT_SEL0
#define Pin_MOSI__0__HSIOM_MASK 0x0000000Fu
#define Pin_MOSI__0__HSIOM_SHIFT 0u
#define Pin_MOSI__0__INTCFG CYREG_PRT0_INTCFG
#define Pin_MOSI__0__INTSTAT CYREG_PRT0_INTSTAT
#define Pin_MOSI__0__MASK 0x01u
#define Pin_MOSI__0__PA__CFG0 CYREG_UDB_PA0_CFG0
#define Pin_MOSI__0__PA__CFG1 CYREG_UDB_PA0_CFG1
#define Pin_MOSI__0__PA__CFG10 CYREG_UDB_PA0_CFG10
#define Pin_MOSI__0__PA__CFG11 CYREG_UDB_PA0_CFG11
#define Pin_MOSI__0__PA__CFG12 CYREG_UDB_PA0_CFG12
#define Pin_MOSI__0__PA__CFG13 CYREG_UDB_PA0_CFG13
#define Pin_MOSI__0__PA__CFG14 CYREG_UDB_PA0_CFG14
#define Pin_MOSI__0__PA__CFG2 CYREG_UDB_PA0_CFG2
#define Pin_MOSI__0__PA__CFG3 CYREG_UDB_PA0_CFG3
#define Pin_MOSI__0__PA__CFG4 CYREG_UDB_PA0_CFG4
#define Pin_MOSI__0__PA__CFG5 CYREG_UDB_PA0_CFG5
#define Pin_MOSI__0__PA__CFG6 CYREG_UDB_PA0_CFG6
#define Pin_MOSI__0__PA__CFG7 CYREG_UDB_PA0_CFG7
#define Pin_MOSI__0__PA__CFG8 CYREG_UDB_PA0_CFG8
#define Pin_MOSI__0__PA__CFG9 CYREG_UDB_PA0_CFG9
#define Pin_MOSI__0__PC CYREG_PRT0_PC
#define Pin_MOSI__0__PC2 CYREG_PRT0_PC2
#define Pin_MOSI__0__PORT 0u
#define Pin_MOSI__0__PS CYREG_PRT0_PS
#define Pin_MOSI__0__SHIFT 0
#define Pin_MOSI__DR CYREG_PRT0_DR
#define Pin_MOSI__INTCFG CYREG_PRT0_INTCFG
#define Pin_MOSI__INTSTAT CYREG_PRT0_INTSTAT
#define Pin_MOSI__MASK 0x01u
#define Pin_MOSI__PA__CFG0 CYREG_UDB_PA0_CFG0
#define Pin_MOSI__PA__CFG1 CYREG_UDB_PA0_CFG1
#define Pin_MOSI__PA__CFG10 CYREG_UDB_PA0_CFG10
#define Pin_MOSI__PA__CFG11 CYREG_UDB_PA0_CFG11
#define Pin_MOSI__PA__CFG12 CYREG_UDB_PA0_CFG12
#define Pin_MOSI__PA__CFG13 CYREG_UDB_PA0_CFG13
#define Pin_MOSI__PA__CFG14 CYREG_UDB_PA0_CFG14
#define Pin_MOSI__PA__CFG2 CYREG_UDB_PA0_CFG2
#define Pin_MOSI__PA__CFG3 CYREG_UDB_PA0_CFG3
#define Pin_MOSI__PA__CFG4 CYREG_UDB_PA0_CFG4
#define Pin_MOSI__PA__CFG5 CYREG_UDB_PA0_CFG5
#define Pin_MOSI__PA__CFG6 CYREG_UDB_PA0_CFG6
#define Pin_MOSI__PA__CFG7 CYREG_UDB_PA0_CFG7
#define Pin_MOSI__PA__CFG8 CYREG_UDB_PA0_CFG8
#define Pin_MOSI__PA__CFG9 CYREG_UDB_PA0_CFG9
#define Pin_MOSI__PC CYREG_PRT0_PC
#define Pin_MOSI__PC2 CYREG_PRT0_PC2
#define Pin_MOSI__PORT 0u
#define Pin_MOSI__PS CYREG_PRT0_PS
#define Pin_MOSI__SHIFT 0

/* Pin_SCLK */
#define Pin_SCLK__0__DM__MASK 0x38u
#define Pin_SCLK__0__DM__SHIFT 3
#define Pin_SCLK__0__DR CYREG_PRT0_DR
#define Pin_SCLK__0__HSIOM CYREG_HSIOM_PORT_SEL0
#define Pin_SCLK__0__HSIOM_MASK 0x000000F0u
#define Pin_SCLK__0__HSIOM_SHIFT 4u
#define Pin_SCLK__0__INTCFG CYREG_PRT0_INTCFG
#define Pin_SCLK__0__INTSTAT CYREG_PRT0_INTSTAT
#define Pin_SCLK__0__MASK 0x02u
#define Pin_SCLK__0__PA__CFG0 CYREG_UDB_PA0_CFG0
#define Pin_SCLK__0__PA__CFG1 CYREG_UDB_PA0_CFG1
#define Pin_SCLK__0__PA__CFG10 CYREG_UDB_PA0_CFG10
#define Pin_SCLK__0__PA__CFG11 CYREG_UDB_PA0_CFG11
#define Pin_SCLK__0__PA__CFG12 CYREG_UDB_PA0_CFG12
#define Pin_SCLK__0__PA__CFG13 CYREG_UDB_PA0_CFG13
#define Pin_SCLK__0__PA__CFG14 CYREG_UDB_PA0_CFG14
#define Pin_SCLK__0__PA__CFG2 CYREG_UDB_PA0_CFG2
#define Pin_SCLK__0__PA__CFG3 CYREG_UDB_PA0_CFG3
#define Pin_SCLK__0__PA__CFG4 CYREG_UDB_PA0_CFG4
#define Pin_SCLK__0__PA__CFG5 CYREG_UDB_PA0_CFG5
#define Pin_SCLK__0__PA__CFG6 CYREG_UDB_PA0_CFG6
#define Pin_SCLK__0__PA__CFG7 CYREG_UDB_PA0_CFG7
#define Pin_SCLK__0__PA__CFG8 CYREG_UDB_PA0_CFG8
#define Pin_SCLK__0__PA__CFG9 CYREG_UDB_PA0_CFG9
#define Pin_SCLK__0__PC CYREG_PRT0_PC
#define Pin_SCLK__0__PC2 CYREG_PRT0_PC2
#define Pin_SCLK__0__PORT 0u
#define Pin_SCLK__0__PS CYREG_PRT0_PS
#define Pin_SCLK__0__SHIFT 1
#define Pin_SCLK__DR CYREG_PRT0_DR
#define Pin_SCLK__INTCFG CYREG_PRT0_INTCFG
#define Pin_SCLK__INTSTAT CYREG_PRT0_INTSTAT
#define Pin_SCLK__MASK 0x02u
#define Pin_SCLK__PA__CFG0 CYREG_UDB_PA0_CFG0
#define Pin_SCLK__PA__CFG1 CYREG_UDB_PA0_CFG1
#define Pin_SCLK__PA__CFG10 CYREG_UDB_PA0_CFG10
#define Pin_SCLK__PA__CFG11 CYREG_UDB_PA0_CFG11
#define Pin_SCLK__PA__CFG12 CYREG_UDB_PA0_CFG12
#define Pin_SCLK__PA__CFG13 CYREG_UDB_PA0_CFG13
#define Pin_SCLK__PA__CFG14 CYREG_UDB_PA0_CFG14
#define Pin_SCLK__PA__CFG2 CYREG_UDB_PA0_CFG2
#define Pin_SCLK__PA__CFG3 CYREG_UDB_PA0_CFG3
#define Pin_SCLK__PA__CFG4 CYREG_UDB_PA0_CFG4
#define Pin_SCLK__PA__CFG5 CYREG_UDB_PA0_CFG5
#define Pin_SCLK__PA__CFG6 CYREG_UDB_PA0_CFG6
#define Pin_SCLK__PA__CFG7 CYREG_UDB_PA0_CFG7
#define Pin_SCLK__PA__CFG8 CYREG_UDB_PA0_CFG8
#define Pin_SCLK__PA__CFG9 CYREG_UDB_PA0_CFG9
#define Pin_SCLK__PC CYREG_PRT0_PC
#define Pin_SCLK__PC2 CYREG_PRT0_PC2
#define Pin_SCLK__PORT 0u
#define Pin_SCLK__PS CYREG_PRT0_PS
#define Pin_SCLK__SHIFT 1

/* Pin_Button */
#define Pin_Button__0__DM__MASK 0x07u
#define Pin_Button__0__DM__SHIFT 0
#define Pin_Button__0__DR CYREG_PRT2_DR
#define Pin_Button__0__HSIOM CYREG_HSIOM_PORT_SEL2
#define Pin_Button__0__HSIOM_MASK 0x0000000Fu
#define Pin_Button__0__HSIOM_SHIFT 0u
#define Pin_Button__0__INTCFG CYREG_PRT2_INTCFG
#define Pin_Button__0__INTSTAT CYREG_PRT2_INTSTAT
#define Pin_Button__0__MASK 0x01u
#define Pin_Button__0__PA__CFG0 CYREG_UDB_PA2_CFG0
#define Pin_Button__0__PA__CFG1 CYREG_UDB_PA2_CFG1
#define Pin_Button__0__PA__CFG10 CYREG_UDB_PA2_CFG10
#define Pin_Button__0__PA__CFG11 CYREG_UDB_PA2_CFG11
#define Pin_Button__0__PA__CFG12 CYREG_UDB_PA2_CFG12
#define Pin_Button__0__PA__CFG13 CYREG_UDB_PA2_CFG13
#define Pin_Button__0__PA__CFG14 CYREG_UDB_PA2_CFG14
#define Pin_Button__0__PA__CFG2 CYREG_UDB_PA2_CFG2
#define Pin_Button__0__PA__CFG3 CYREG_UDB_PA2_CFG3
#define Pin_Button__0__PA__CFG4 CYREG_UDB_PA2_CFG4
#define Pin_Button__0__PA__CFG5 CYREG_UDB_PA2_CFG5
#define Pin_Button__0__PA__CFG6 CYREG_UDB_PA2_CFG6
#define Pin_Button__0__PA__CFG7 CYREG_UDB_PA2_CFG7
#define Pin_Button__0__PA__CFG8 CYREG_UDB_PA2_CFG8
#define Pin_Button__0__PA__CFG9 CYREG_UDB_PA2_CFG9
#define Pin_Button__0__PC CYREG_PRT2_PC
#define Pin_Button__0__PC2 CYREG_PRT2_PC2
#define Pin_Button__0__PORT 2u
#define Pin_Button__0__PS CYREG_PRT2_PS
#define Pin_Button__0__SHIFT 0
#define Pin_Button__1__DM__MASK 0x38u
#define Pin_Button__1__DM__SHIFT 3
#define Pin_Button__1__DR CYREG_PRT2_DR
#define Pin_Button__1__HSIOM CYREG_HSIOM_PORT_SEL2
#define Pin_Button__1__HSIOM_MASK 0x000000F0u
#define Pin_Button__1__HSIOM_SHIFT 4u
#define Pin_Button__1__INTCFG CYREG_PRT2_INTCFG
#define Pin_Button__1__INTSTAT CYREG_PRT2_INTSTAT
#define Pin_Button__1__MASK 0x02u
#define Pin_Button__1__PA__CFG0 CYREG_UDB_PA2_CFG0
#define Pin_Button__1__PA__CFG1 CYREG_UDB_PA2_CFG1
#define Pin_Button__1__PA__CFG10 CYREG_UDB_PA2_CFG10
#define Pin_Button__1__PA__CFG11 CYREG_UDB_PA2_CFG11
#define Pin_Button__1__PA__CFG12 CYREG_UDB_PA2_CFG12
#define Pin_Button__1__PA__CFG13 CYREG_UDB_PA2_CFG13
#define Pin_Button__1__PA__CFG14 CYREG_UDB_PA2_CFG14
#define Pin_Button__1__PA__CFG2 CYREG_UDB_PA2_CFG2
#define Pin_Button__1__PA__CFG3 CYREG_UDB_PA2_CFG3
#define Pin_Button__1__PA__CFG4 CYREG_UDB_PA2_CFG4
#define Pin_Button__1__PA__CFG5 CYREG_UDB_PA2_CFG5
#define Pin_Button__1__PA__CFG6 CYREG_UDB_PA2_CFG6
#define Pin_Button__1__PA__CFG7 CYREG_UDB_PA2_CFG7
#define Pin_Button__1__PA__CFG8 CYREG_UDB_PA2_CFG8
#define Pin_Button__1__PA__CFG9 CYREG_UDB_PA2_CFG9
#define Pin_Button__1__PC CYREG_PRT2_PC
#define Pin_Button__1__PC2 CYREG_PRT2_PC2
#define Pin_Button__1__PORT 2u
#define Pin_Button__1__PS CYREG_PRT2_PS
#define Pin_Button__1__SHIFT 1
#define Pin_Button__2__DM__MASK 0x1C0u
#define Pin_Button__2__DM__SHIFT 6
#define Pin_Button__2__DR CYREG_PRT2_DR
#define Pin_Button__2__HSIOM CYREG_HSIOM_PORT_SEL2
#define Pin_Button__2__HSIOM_MASK 0x00000F00u
#define Pin_Button__2__HSIOM_SHIFT 8u
#define Pin_Button__2__INTCFG CYREG_PRT2_INTCFG
#define Pin_Button__2__INTSTAT CYREG_PRT2_INTSTAT
#define Pin_Button__2__MASK 0x04u
#define Pin_Button__2__PA__CFG0 CYREG_UDB_PA2_CFG0
#define Pin_Button__2__PA__CFG1 CYREG_UDB_PA2_CFG1
#define Pin_Button__2__PA__CFG10 CYREG_UDB_PA2_CFG10
#define Pin_Button__2__PA__CFG11 CYREG_UDB_PA2_CFG11
#define Pin_Button__2__PA__CFG12 CYREG_UDB_PA2_CFG12
#define Pin_Button__2__PA__CFG13 CYREG_UDB_PA2_CFG13
#define Pin_Button__2__PA__CFG14 CYREG_UDB_PA2_CFG14
#define Pin_Button__2__PA__CFG2 CYREG_UDB_PA2_CFG2
#define Pin_Button__2__PA__CFG3 CYREG_UDB_PA2_CFG3
#define Pin_Button__2__PA__CFG4 CYREG_UDB_PA2_CFG4
#define Pin_Button__2__PA__CFG5 CYREG_UDB_PA2_CFG5
#define Pin_Button__2__PA__CFG6 CYREG_UDB_PA2_CFG6
#define Pin_Button__2__PA__CFG7 CYREG_UDB_PA2_CFG7
#define Pin_Button__2__PA__CFG8 CYREG_UDB_PA2_CFG8
#define Pin_Button__2__PA__CFG9 CYREG_UDB_PA2_CFG9
#define Pin_Button__2__PC CYREG_PRT2_PC
#define Pin_Button__2__PC2 CYREG_PRT2_PC2
#define Pin_Button__2__PORT 2u
#define Pin_Button__2__PS CYREG_PRT2_PS
#define Pin_Button__2__SHIFT 2
#define Pin_Button__3__DM__MASK 0xE00u
#define Pin_Button__3__DM__SHIFT 9
#define Pin_Button__3__DR CYREG_PRT2_DR
#define Pin_Button__3__HSIOM CYREG_HSIOM_PORT_SEL2
#define Pin_Button__3__HSIOM_MASK 0x0000F000u
#define Pin_Button__3__HSIOM_SHIFT 12u
#define Pin_Button__3__INTCFG CYREG_PRT2_INTCFG
#define Pin_Button__3__INTSTAT CYREG_PRT2_INTSTAT
#define Pin_Button__3__MASK 0x08u
#define Pin_Button__3__PA__CFG0 CYREG_UDB_PA2_CFG0
#define Pin_Button__3__PA__CFG1 CYREG_UDB_PA2_CFG1
#define Pin_Button__3__PA__CFG10 CYREG_UDB_PA2_CFG10
#define Pin_Button__3__PA__CFG11 CYREG_UDB_PA2_CFG11
#define Pin_Button__3__PA__CFG12 CYREG_UDB_PA2_CFG12
#define Pin_Button__3__PA__CFG13 CYREG_UDB_PA2_CFG13
#define Pin_Button__3__PA__CFG14 CYREG_UDB_PA2_CFG14
#define Pin_Button__3__PA__CFG2 CYREG_UDB_PA2_CFG2
#define Pin_Button__3__PA__CFG3 CYREG_UDB_PA2_CFG3
#define Pin_Button__3__PA__CFG4 CYREG_UDB_PA2_CFG4
#define Pin_Button__3__PA__CFG5 CYREG_UDB_PA2_CFG5
#define Pin_Button__3__PA__CFG6 CYREG_UDB_PA2_CFG6
#define Pin_Button__3__PA__CFG7 CYREG_UDB_PA2_CFG7
#define Pin_Button__3__PA__CFG8 CYREG_UDB_PA2_CFG8
#define Pin_Button__3__PA__CFG9 CYREG_UDB_PA2_CFG9
#define Pin_Button__3__PC CYREG_PRT2_PC
#define Pin_Button__3__PC2 CYREG_PRT2_PC2
#define Pin_Button__3__PORT 2u
#define Pin_Button__3__PS CYREG_PRT2_PS
#define Pin_Button__3__SHIFT 3
#define Pin_Button__DR CYREG_PRT2_DR
#define Pin_Button__INTCFG CYREG_PRT2_INTCFG
#define Pin_Button__INTSTAT CYREG_PRT2_INTSTAT
#define Pin_Button__MASK 0x0Fu
#define Pin_Button__PA__CFG0 CYREG_UDB_PA2_CFG0
#define Pin_Button__PA__CFG1 CYREG_UDB_PA2_CFG1
#define Pin_Button__PA__CFG10 CYREG_UDB_PA2_CFG10
#define Pin_Button__PA__CFG11 CYREG_UDB_PA2_CFG11
#define Pin_Button__PA__CFG12 CYREG_UDB_PA2_CFG12
#define Pin_Button__PA__CFG13 CYREG_UDB_PA2_CFG13
#define Pin_Button__PA__CFG14 CYREG_UDB_PA2_CFG14
#define Pin_Button__PA__CFG2 CYREG_UDB_PA2_CFG2
#define Pin_Button__PA__CFG3 CYREG_UDB_PA2_CFG3
#define Pin_Button__PA__CFG4 CYREG_UDB_PA2_CFG4
#define Pin_Button__PA__CFG5 CYREG_UDB_PA2_CFG5
#define Pin_Button__PA__CFG6 CYREG_UDB_PA2_CFG6
#define Pin_Button__PA__CFG7 CYREG_UDB_PA2_CFG7
#define Pin_Button__PA__CFG8 CYREG_UDB_PA2_CFG8
#define Pin_Button__PA__CFG9 CYREG_UDB_PA2_CFG9
#define Pin_Button__PC CYREG_PRT2_PC
#define Pin_Button__PC2 CYREG_PRT2_PC2
#define Pin_Button__PORT 2u
#define Pin_Button__PS CYREG_PRT2_PS
#define Pin_Button__SHIFT 0
#define Pin_Button__SNAP CYREG_PRT2_INTSTAT

/* isr_button */
#define isr_button__INTC_CLR_EN_REG CYREG_CM0_ICER
#define isr_button__INTC_CLR_PD_REG CYREG_CM0_ICPR
#define isr_button__INTC_MASK 0x04u
#define isr_button__INTC_NUMBER 2u
#define isr_button__INTC_PRIOR_MASK 0xC00000u
#define isr_button__INTC_PRIOR_NUM 3u
#define isr_button__INTC_PRIOR_REG CYREG_CM0_IPR0
#define isr_button__INTC_SET_EN_REG CYREG_CM0_ISER
#define isr_button__INTC_SET_PD_REG CYREG_CM0_ISPR

/* Pin_LED_Red */
#define Pin_LED_Red__0__DM__MASK 0x7000u
#define Pin_LED_Red__0__DM__SHIFT 12
#define Pin_LED_Red__0__DR CYREG_PRT1_DR
#define Pin_LED_Red__0__HSIOM CYREG_HSIOM_PORT_SEL1
#define Pin_LED_Red__0__HSIOM_MASK 0x000F0000u
#define Pin_LED_Red__0__HSIOM_SHIFT 16u
#define Pin_LED_Red__0__INTCFG CYREG_PRT1_INTCFG
#define Pin_LED_Red__0__INTSTAT CYREG_PRT1_INTSTAT
#define Pin_LED_Red__0__MASK 0x10u
#define Pin_LED_Red__0__PA__CFG0 CYREG_UDB_PA1_CFG0
#define Pin_LED_Red__0__PA__CFG1 CYREG_UDB_PA1_CFG1
#define Pin_LED_Red__0__PA__CFG10 CYREG_UDB_PA1_CFG10
#define Pin_LED_Red__0__PA__CFG11 CYREG_UDB_PA1_CFG11
#define Pin_LED_Red__0__PA__CFG12 CYREG_UDB_PA1_CFG12
#define Pin_LED_Red__0__PA__CFG13 CYREG_UDB_PA1_CFG13
#define Pin_LED_Red__0__PA__CFG14 CYREG_UDB_PA1_CFG14
#define Pin_LED_Red__0__PA__CFG2 CYREG_UDB_PA1_CFG2
#define Pin_LED_Red__0__PA__CFG3 CYREG_UDB_PA1_CFG3
#define Pin_LED_Red__0__PA__CFG4 CYREG_UDB_PA1_CFG4
#define Pin_LED_Red__0__PA__CFG5 CYREG_UDB_PA1_CFG5
#define Pin_LED_Red__0__PA__CFG6 CYREG_UDB_PA1_CFG6
#define Pin_LED_Red__0__PA__CFG7 CYREG_UDB_PA1_CFG7
#define Pin_LED_Red__0__PA__CFG8 CYREG_UDB_PA1_CFG8
#define Pin_LED_Red__0__PA__CFG9 CYREG_UDB_PA1_CFG9
#define Pin_LED_Red__0__PC CYREG_PRT1_PC
#define Pin_LED_Red__0__PC2 CYREG_PRT1_PC2
#define Pin_LED_Red__0__PORT 1u
#define Pin_LED_Red__0__PS CYREG_PRT1_PS
#define Pin_LED_Red__0__SHIFT 4
#define Pin_LED_Red__DR CYREG_PRT1_DR
#define Pin_LED_Red__INTCFG CYREG_PRT1_INTCFG
#define Pin_LED_Red__INTSTAT CYREG_PRT1_INTSTAT
#define Pin_LED_Red__MASK 0x10u
#define Pin_LED_Red__PA__CFG0 CYREG_UDB_PA1_CFG0
#define Pin_LED_Red__PA__CFG1 CYREG_UDB_PA1_CFG1
#define Pin_LED_Red__PA__CFG10 CYREG_UDB_PA1_CFG10
#define Pin_LED_Red__PA__CFG11 CYREG_UDB_PA1_CFG11
#define Pin_LED_Red__PA__CFG12 CYREG_UDB_PA1_CFG12
#define Pin_LED_Red__PA__CFG13 CYREG_UDB_PA1_CFG13
#define Pin_LED_Red__PA__CFG14 CYREG_UDB_PA1_CFG14
#define Pin_LED_Red__PA__CFG2 CYREG_UDB_PA1_CFG2
#define Pin_LED_Red__PA__CFG3 CYREG_UDB_PA1_CFG3
#define Pin_LED_Red__PA__CFG4 CYREG_UDB_PA1_CFG4
#define Pin_LED_Red__PA__CFG5 CYREG_UDB_PA1_CFG5
#define Pin_LED_Red__PA__CFG6 CYREG_UDB_PA1_CFG6
#define Pin_LED_Red__PA__CFG7 CYREG_UDB_PA1_CFG7
#define Pin_LED_Red__PA__CFG8 CYREG_UDB_PA1_CFG8
#define Pin_LED_Red__PA__CFG9 CYREG_UDB_PA1_CFG9
#define Pin_LED_Red__PC CYREG_PRT1_PC
#define Pin_LED_Red__PC2 CYREG_PRT1_PC2
#define Pin_LED_Red__PORT 1u
#define Pin_LED_Red__PS CYREG_PRT1_PS
#define Pin_LED_Red__SHIFT 4

/* Pin_LED_Debug */
#define Pin_LED_Debug__0__DM__MASK 0x1C0000u
#define Pin_LED_Debug__0__DM__SHIFT 18
#define Pin_LED_Debug__0__DR CYREG_PRT1_DR
#define Pin_LED_Debug__0__HSIOM CYREG_HSIOM_PORT_SEL1
#define Pin_LED_Debug__0__HSIOM_MASK 0x0F000000u
#define Pin_LED_Debug__0__HSIOM_SHIFT 24u
#define Pin_LED_Debug__0__INTCFG CYREG_PRT1_INTCFG
#define Pin_LED_Debug__0__INTSTAT CYREG_PRT1_INTSTAT
#define Pin_LED_Debug__0__MASK 0x40u
#define Pin_LED_Debug__0__PA__CFG0 CYREG_UDB_PA1_CFG0
#define Pin_LED_Debug__0__PA__CFG1 CYREG_UDB_PA1_CFG1
#define Pin_LED_Debug__0__PA__CFG10 CYREG_UDB_PA1_CFG10
#define Pin_LED_Debug__0__PA__CFG11 CYREG_UDB_PA1_CFG11
#define Pin_LED_Debug__0__PA__CFG12 CYREG_UDB_PA1_CFG12
#define Pin_LED_Debug__0__PA__CFG13 CYREG_UDB_PA1_CFG13
#define Pin_LED_Debug__0__PA__CFG14 CYREG_UDB_PA1_CFG14
#define Pin_LED_Debug__0__PA__CFG2 CYREG_UDB_PA1_CFG2
#define Pin_LED_Debug__0__PA__CFG3 CYREG_UDB_PA1_CFG3
#define Pin_LED_Debug__0__PA__CFG4 CYREG_UDB_PA1_CFG4
#define Pin_LED_Debug__0__PA__CFG5 CYREG_UDB_PA1_CFG5
#define Pin_LED_Debug__0__PA__CFG6 CYREG_UDB_PA1_CFG6
#define Pin_LED_Debug__0__PA__CFG7 CYREG_UDB_PA1_CFG7
#define Pin_LED_Debug__0__PA__CFG8 CYREG_UDB_PA1_CFG8
#define Pin_LED_Debug__0__PA__CFG9 CYREG_UDB_PA1_CFG9
#define Pin_LED_Debug__0__PC CYREG_PRT1_PC
#define Pin_LED_Debug__0__PC2 CYREG_PRT1_PC2
#define Pin_LED_Debug__0__PORT 1u
#define Pin_LED_Debug__0__PS CYREG_PRT1_PS
#define Pin_LED_Debug__0__SHIFT 6
#define Pin_LED_Debug__DR CYREG_PRT1_DR
#define Pin_LED_Debug__INTCFG CYREG_PRT1_INTCFG
#define Pin_LED_Debug__INTSTAT CYREG_PRT1_INTSTAT
#define Pin_LED_Debug__MASK 0x40u
#define Pin_LED_Debug__PA__CFG0 CYREG_UDB_PA1_CFG0
#define Pin_LED_Debug__PA__CFG1 CYREG_UDB_PA1_CFG1
#define Pin_LED_Debug__PA__CFG10 CYREG_UDB_PA1_CFG10
#define Pin_LED_Debug__PA__CFG11 CYREG_UDB_PA1_CFG11
#define Pin_LED_Debug__PA__CFG12 CYREG_UDB_PA1_CFG12
#define Pin_LED_Debug__PA__CFG13 CYREG_UDB_PA1_CFG13
#define Pin_LED_Debug__PA__CFG14 CYREG_UDB_PA1_CFG14
#define Pin_LED_Debug__PA__CFG2 CYREG_UDB_PA1_CFG2
#define Pin_LED_Debug__PA__CFG3 CYREG_UDB_PA1_CFG3
#define Pin_LED_Debug__PA__CFG4 CYREG_UDB_PA1_CFG4
#define Pin_LED_Debug__PA__CFG5 CYREG_UDB_PA1_CFG5
#define Pin_LED_Debug__PA__CFG6 CYREG_UDB_PA1_CFG6
#define Pin_LED_Debug__PA__CFG7 CYREG_UDB_PA1_CFG7
#define Pin_LED_Debug__PA__CFG8 CYREG_UDB_PA1_CFG8
#define Pin_LED_Debug__PA__CFG9 CYREG_UDB_PA1_CFG9
#define Pin_LED_Debug__PC CYREG_PRT1_PC
#define Pin_LED_Debug__PC2 CYREG_PRT1_PC2
#define Pin_LED_Debug__PORT 1u
#define Pin_LED_Debug__PS CYREG_PRT1_PS
#define Pin_LED_Debug__SHIFT 6

/* Pin_LED_Green */
#define Pin_LED_Green__0__DM__MASK 0xE00u
#define Pin_LED_Green__0__DM__SHIFT 9
#define Pin_LED_Green__0__DR CYREG_PRT1_DR
#define Pin_LED_Green__0__HSIOM CYREG_HSIOM_PORT_SEL1
#define Pin_LED_Green__0__HSIOM_MASK 0x0000F000u
#define Pin_LED_Green__0__HSIOM_SHIFT 12u
#define Pin_LED_Green__0__INTCFG CYREG_PRT1_INTCFG
#define Pin_LED_Green__0__INTSTAT CYREG_PRT1_INTSTAT
#define Pin_LED_Green__0__MASK 0x08u
#define Pin_LED_Green__0__PA__CFG0 CYREG_UDB_PA1_CFG0
#define Pin_LED_Green__0__PA__CFG1 CYREG_UDB_PA1_CFG1
#define Pin_LED_Green__0__PA__CFG10 CYREG_UDB_PA1_CFG10
#define Pin_LED_Green__0__PA__CFG11 CYREG_UDB_PA1_CFG11
#define Pin_LED_Green__0__PA__CFG12 CYREG_UDB_PA1_CFG12
#define Pin_LED_Green__0__PA__CFG13 CYREG_UDB_PA1_CFG13
#define Pin_LED_Green__0__PA__CFG14 CYREG_UDB_PA1_CFG14
#define Pin_LED_Green__0__PA__CFG2 CYREG_UDB_PA1_CFG2
#define Pin_LED_Green__0__PA__CFG3 CYREG_UDB_PA1_CFG3
#define Pin_LED_Green__0__PA__CFG4 CYREG_UDB_PA1_CFG4
#define Pin_LED_Green__0__PA__CFG5 CYREG_UDB_PA1_CFG5
#define Pin_LED_Green__0__PA__CFG6 CYREG_UDB_PA1_CFG6
#define Pin_LED_Green__0__PA__CFG7 CYREG_UDB_PA1_CFG7
#define Pin_LED_Green__0__PA__CFG8 CYREG_UDB_PA1_CFG8
#define Pin_LED_Green__0__PA__CFG9 CYREG_UDB_PA1_CFG9
#define Pin_LED_Green__0__PC CYREG_PRT1_PC
#define Pin_LED_Green__0__PC2 CYREG_PRT1_PC2
#define Pin_LED_Green__0__PORT 1u
#define Pin_LED_Green__0__PS CYREG_PRT1_PS
#define Pin_LED_Green__0__SHIFT 3
#define Pin_LED_Green__DR CYREG_PRT1_DR
#define Pin_LED_Green__INTCFG CYREG_PRT1_INTCFG
#define Pin_LED_Green__INTSTAT CYREG_PRT1_INTSTAT
#define Pin_LED_Green__MASK 0x08u
#define Pin_LED_Green__PA__CFG0 CYREG_UDB_PA1_CFG0
#define Pin_LED_Green__PA__CFG1 CYREG_UDB_PA1_CFG1
#define Pin_LED_Green__PA__CFG10 CYREG_UDB_PA1_CFG10
#define Pin_LED_Green__PA__CFG11 CYREG_UDB_PA1_CFG11
#define Pin_LED_Green__PA__CFG12 CYREG_UDB_PA1_CFG12
#define Pin_LED_Green__PA__CFG13 CYREG_UDB_PA1_CFG13
#define Pin_LED_Green__PA__CFG14 CYREG_UDB_PA1_CFG14
#define Pin_LED_Green__PA__CFG2 CYREG_UDB_PA1_CFG2
#define Pin_LED_Green__PA__CFG3 CYREG_UDB_PA1_CFG3
#define Pin_LED_Green__PA__CFG4 CYREG_UDB_PA1_CFG4
#define Pin_LED_Green__PA__CFG5 CYREG_UDB_PA1_CFG5
#define Pin_LED_Green__PA__CFG6 CYREG_UDB_PA1_CFG6
#define Pin_LED_Green__PA__CFG7 CYREG_UDB_PA1_CFG7
#define Pin_LED_Green__PA__CFG8 CYREG_UDB_PA1_CFG8
#define Pin_LED_Green__PA__CFG9 CYREG_UDB_PA1_CFG9
#define Pin_LED_Green__PC CYREG_PRT1_PC
#define Pin_LED_Green__PC2 CYREG_PRT1_PC2
#define Pin_LED_Green__PORT 1u
#define Pin_LED_Green__PS CYREG_PRT1_PS
#define Pin_LED_Green__SHIFT 3

/* Pin_LED_Yellow */
#define Pin_LED_Yellow__0__DM__MASK 0x38000u
#define Pin_LED_Yellow__0__DM__SHIFT 15
#define Pin_LED_Yellow__0__DR CYREG_PRT1_DR
#define Pin_LED_Yellow__0__HSIOM CYREG_HSIOM_PORT_SEL1
#define Pin_LED_Yellow__0__HSIOM_MASK 0x00F00000u
#define Pin_LED_Yellow__0__HSIOM_SHIFT 20u
#define Pin_LED_Yellow__0__INTCFG CYREG_PRT1_INTCFG
#define Pin_LED_Yellow__0__INTSTAT CYREG_PRT1_INTSTAT
#define Pin_LED_Yellow__0__MASK 0x20u
#define Pin_LED_Yellow__0__PA__CFG0 CYREG_UDB_PA1_CFG0
#define Pin_LED_Yellow__0__PA__CFG1 CYREG_UDB_PA1_CFG1
#define Pin_LED_Yellow__0__PA__CFG10 CYREG_UDB_PA1_CFG10
#define Pin_LED_Yellow__0__PA__CFG11 CYREG_UDB_PA1_CFG11
#define Pin_LED_Yellow__0__PA__CFG12 CYREG_UDB_PA1_CFG12
#define Pin_LED_Yellow__0__PA__CFG13 CYREG_UDB_PA1_CFG13
#define Pin_LED_Yellow__0__PA__CFG14 CYREG_UDB_PA1_CFG14
#define Pin_LED_Yellow__0__PA__CFG2 CYREG_UDB_PA1_CFG2
#define Pin_LED_Yellow__0__PA__CFG3 CYREG_UDB_PA1_CFG3
#define Pin_LED_Yellow__0__PA__CFG4 CYREG_UDB_PA1_CFG4
#define Pin_LED_Yellow__0__PA__CFG5 CYREG_UDB_PA1_CFG5
#define Pin_LED_Yellow__0__PA__CFG6 CYREG_UDB_PA1_CFG6
#define Pin_LED_Yellow__0__PA__CFG7 CYREG_UDB_PA1_CFG7
#define Pin_LED_Yellow__0__PA__CFG8 CYREG_UDB_PA1_CFG8
#define Pin_LED_Yellow__0__PA__CFG9 CYREG_UDB_PA1_CFG9
#define Pin_LED_Yellow__0__PC CYREG_PRT1_PC
#define Pin_LED_Yellow__0__PC2 CYREG_PRT1_PC2
#define Pin_LED_Yellow__0__PORT 1u
#define Pin_LED_Yellow__0__PS CYREG_PRT1_PS
#define Pin_LED_Yellow__0__SHIFT 5
#define Pin_LED_Yellow__DR CYREG_PRT1_DR
#define Pin_LED_Yellow__INTCFG CYREG_PRT1_INTCFG
#define Pin_LED_Yellow__INTSTAT CYREG_PRT1_INTSTAT
#define Pin_LED_Yellow__MASK 0x20u
#define Pin_LED_Yellow__PA__CFG0 CYREG_UDB_PA1_CFG0
#define Pin_LED_Yellow__PA__CFG1 CYREG_UDB_PA1_CFG1
#define Pin_LED_Yellow__PA__CFG10 CYREG_UDB_PA1_CFG10
#define Pin_LED_Yellow__PA__CFG11 CYREG_UDB_PA1_CFG11
#define Pin_LED_Yellow__PA__CFG12 CYREG_UDB_PA1_CFG12
#define Pin_LED_Yellow__PA__CFG13 CYREG_UDB_PA1_CFG13
#define Pin_LED_Yellow__PA__CFG14 CYREG_UDB_PA1_CFG14
#define Pin_LED_Yellow__PA__CFG2 CYREG_UDB_PA1_CFG2
#define Pin_LED_Yellow__PA__CFG3 CYREG_UDB_PA1_CFG3
#define Pin_LED_Yellow__PA__CFG4 CYREG_UDB_PA1_CFG4
#define Pin_LED_Yellow__PA__CFG5 CYREG_UDB_PA1_CFG5
#define Pin_LED_Yellow__PA__CFG6 CYREG_UDB_PA1_CFG6
#define Pin_LED_Yellow__PA__CFG7 CYREG_UDB_PA1_CFG7
#define Pin_LED_Yellow__PA__CFG8 CYREG_UDB_PA1_CFG8
#define Pin_LED_Yellow__PA__CFG9 CYREG_UDB_PA1_CFG9
#define Pin_LED_Yellow__PC CYREG_PRT1_PC
#define Pin_LED_Yellow__PC2 CYREG_PRT1_PC2
#define Pin_LED_Yellow__PORT 1u
#define Pin_LED_Yellow__PS CYREG_PRT1_PS
#define Pin_LED_Yellow__SHIFT 5

/* Miscellaneous */
#define CYDEV_BCLK__HFCLK__HZ 24000000U
#define CYDEV_BCLK__HFCLK__KHZ 24000U
#define CYDEV_BCLK__HFCLK__MHZ 24U
#define CYDEV_BCLK__SYSCLK__HZ 24000000U
#define CYDEV_BCLK__SYSCLK__KHZ 24000U
#define CYDEV_BCLK__SYSCLK__MHZ 24U
#define CYDEV_CHIP_DIE_LEOPARD 1u
#define CYDEV_CHIP_DIE_PANTHER 4u
#define CYDEV_CHIP_DIE_PSOC4A 2u
#define CYDEV_CHIP_DIE_PSOC5LP 5u
#define CYDEV_CHIP_DIE_UNKNOWN 0u
#define CYDEV_CHIP_FAMILY_PSOC3 1u
#define CYDEV_CHIP_FAMILY_PSOC4 2u
#define CYDEV_CHIP_FAMILY_PSOC5 3u
#define CYDEV_CHIP_FAMILY_UNKNOWN 0u
#define CYDEV_CHIP_FAMILY_USED CYDEV_CHIP_FAMILY_PSOC4
#define CYDEV_CHIP_JTAG_ID 0x04C81193u
#define CYDEV_CHIP_MEMBER_3A 1u
#define CYDEV_CHIP_MEMBER_4A 2u
#define CYDEV_CHIP_MEMBER_4D 3u
#define CYDEV_CHIP_MEMBER_5A 4u
#define CYDEV_CHIP_MEMBER_5B 5u
#define CYDEV_CHIP_MEMBER_UNKNOWN 0u
#define CYDEV_CHIP_MEMBER_USED CYDEV_CHIP_MEMBER_4A
#define CYDEV_CHIP_DIE_EXPECT CYDEV_CHIP_MEMBER_USED
#define CYDEV_CHIP_DIE_ACTUAL CYDEV_CHIP_DIE_EXPECT
#define CYDEV_CHIP_REV_LEOPARD_ES1 0u
#define CYDEV_CHIP_REV_LEOPARD_ES2 1u
#define CYDEV_CHIP_REV_LEOPARD_ES3 3u
#define CYDEV_CHIP_REV_LEOPARD_PRODUCTION 3u
#define CYDEV_CHIP_REV_PANTHER_ES0 0u
#define CYDEV_CHIP_REV_PANTHER_ES1 1u
#define CYDEV_CHIP_REV_PANTHER_PRODUCTION 1u
#define CYDEV_CHIP_REV_PSOC4A_ES0 17u
#define CYDEV_CHIP_REV_PSOC4A_PRODUCTION 17u
#define CYDEV_CHIP_REV_PSOC5LP_ES0 0u
#define CYDEV_CHIP_REV_PSOC5LP_PRODUCTION 0u
#define CYDEV_CHIP_REVISION_3A_ES1 0u
#define CYDEV_CHIP_REVISION_3A_ES2 1u
#define CYDEV_CHIP_REVISION_3A_ES3 3u
#define CYDEV_CHIP_REVISION_3A_PRODUCTION 3u
#define CYDEV_CHIP_REVISION_4A_ES0 17u
#define CYDEV_CHIP_REVISION_4A_PRODUCTION 17u
#define CYDEV_CHIP_REVISION_4D_ES0 0u
#define CYDEV_CHIP_REVISION_4D_PRODUCTION 0u
#define CYDEV_CHIP_REVISION_5A_ES0 0u
#define CYDEV_CHIP_REVISION_5A_ES1 1u
#define CYDEV_CHIP_REVISION_5A_PRODUCTION 1u
#define CYDEV_CHIP_REVISION_5B_ES0 0u
#define CYDEV_CHIP_REVISION_5B_PRODUCTION 0u
#define CYDEV_CHIP_REVISION_USED CYDEV_CHIP_REVISION_4A_PRODUCTION
#define CYDEV_CHIP_REV_EXPECT CYDEV_CHIP_REVISION_USED
#define CYDEV_CONFIG_READ_ACCELERATOR 1
#define CYDEV_CONFIG_UNUSED_IO_AllowButWarn 0
#define CYDEV_CONFIG_UNUSED_IO CYDEV_CONFIG_UNUSED_IO_AllowButWarn
#define CYDEV_CONFIG_UNUSED_IO_AllowWithInfo 1
#define CYDEV_CONFIG_UNUSED_IO_Disallowed 2
#define CYDEV_CONFIGURATION_COMPRESSED 1
#define CYDEV_CONFIGURATION_MODE_COMPRESSED 0
#define CYDEV_CONFIGURATION_MODE CYDEV_CONFIGURATION_MODE_COMPRESSED
#define CYDEV_CONFIGURATION_MODE_DMA 2
#define CYDEV_CONFIGURATION_MODE_UNCOMPRESSED 1
#define CYDEV_DEBUG_PROTECT_KILL 4
#define CYDEV_DEBUG_PROTECT_OPEN 1
#define CYDEV_DEBUG_PROTECT CYDEV_DEBUG_PROTECT_OPEN
#define CYDEV_DEBUG_PROTECT_PROTECTED 2
#define CYDEV_DEBUGGING_DPS_Disable 3
#define CYDEV_DEBUGGING_DPS_SWD 2
#define CYDEV_DEBUGGING_DPS CYDEV_DEBUGGING_DPS_SWD
#define CYDEV_DEBUGGING_ENABLE 1
#define CYDEV_HEAP_SIZE 0x0100
#define CYDEV_PROJ_TYPE 0
#define CYDEV_PROJ_TYPE_BOOTLOADER 1
#define CYDEV_PROJ_TYPE_LOADABLE 2
#define CYDEV_PROJ_TYPE_MULTIAPPBOOTLOADER 3
#define CYDEV_PROJ_TYPE_STANDARD 0
#define CYDEV_STACK_SIZE 0x0400
#define CYDEV_USE_BUNDLED_CMSIS 1
#define CYDEV_VARIABLE_VDDA 1
#define CYDEV_VDDA 3.3
#define CYDEV_VDDA_MV 3300
#define CYDEV_VDDD 3.3
#define CYDEV_VDDD_MV 3300
#define CYIPBLOCK_M0S8_CTBM_VERSION 0
#define CYIPBLOCK_m0s8cpuss_VERSION 0
#define CYIPBLOCK_m0s8csd_VERSION 0
#define CYIPBLOCK_m0s8gpio2_VERSION 0
#define CYIPBLOCK_m0s8hsiom4a_VERSION 0
#define CYIPBLOCK_m0s8lcd_VERSION 0
#define CYIPBLOCK_m0s8lpcomp_VERSION 0
#define CYIPBLOCK_m0s8pclk_VERSION 0
#define CYIPBLOCK_m0s8sar_VERSION 0
#define CYIPBLOCK_m0s8scb_VERSION 0
#define CYIPBLOCK_m0s8srssv2_VERSION 1
#define CYIPBLOCK_m0s8tcpwm_VERSION 0
#define CYIPBLOCK_m0s8udbif_VERSION 0
#define CYIPBLOCK_S8_GPIO_VERSION 2
#define CYDEV_BOOTLOADER_ENABLE 0

#endif /* INCLUDED_CYFITTER_H */
