trehansiddharth/SignAway/Source/PSoC/SignatureVerifier/SignatureVerifier.cydsn/codegentemp/SPI.c

/*******************************************************************************
* File Name: SPI.c
* Version 2.60
*
* Description:
*  This file provides all API functionality of the SPI Slave component.
*
* Note:
*  None.
*
********************************************************************************
* Copyright 2008-2013, Cypress Semiconductor Corporation.  All rights reserved.
* You may use this file only in accordance with the license, terms, conditions,
* disclaimers, and limitations in the end user license agreement accompanying
* the software package with which this file was provided.
*******************************************************************************/

#include "SPI_PVT.h"

#if (SPI_TX_SOFTWARE_BUF_ENABLED)

    volatile uint16 SPI_txBuffer[SPI_TX_BUFFER_SIZE] = {0u};
    volatile uint8 SPI_txBufferRead;
    volatile uint8 SPI_txBufferWrite;
    volatile uint8 SPI_txBufferFull;

#endif /* SPI_TX_SOFTWARE_BUF_ENABLED*/

#if (SPI_RX_SOFTWARE_BUF_ENABLED)

    volatile uint16 SPI_rxBuffer[SPI_RX_BUFFER_SIZE] = {0u};
    volatile uint8 SPI_rxBufferRead;
    volatile uint8 SPI_rxBufferWrite;
    volatile uint8 SPI_rxBufferFull;

#endif /* SPI_RX_SOFTWARE_BUF_ENABLED */

uint8 SPI_initVar = 0u;

volatile uint8 SPI_swStatusTx;
volatile uint8 SPI_swStatusRx;


/*******************************************************************************
* Function Name: SPI_Init
********************************************************************************
*
* Summary:
*  Inits/Restores default SPIS configuration provided with customizer.
*
* Parameters:
*  None.
*
* Return:
*  None.
*
* Side Effects:
*  When this function is called it initializes all of the necessary parameters
*  for execution. i.e. setting the initial interrupt mask, configuring the
*  interrupt service routine, configuring the bit-counter parameters and
*  clearing the FIFO and Status Register.
*
* Reentrant:
*  No.
*
*******************************************************************************/
void SPI_Init(void) 
{
    /*Initialize the Bit counter */
    SPI_COUNTER_PERIOD_REG = SPI_BITCTR_INIT;

    /* ISR initialization */
    #if(SPI_INTERNAL_TX_INT_ENABLED)

        CyIntDisable(SPI_TX_ISR_NUMBER);

        /* Set the ISR to point to the SPI_isr Interrupt. */
        (void)CyIntSetVector(SPI_TX_ISR_NUMBER, &SPI_TX_ISR);

        /* Set the priority. */
        CyIntSetPriority(SPI_TX_ISR_NUMBER, SPI_TX_ISR_PRIORITY);

    #endif /* SPI_INTERNAL_TX_INT_ENABLED */

    #if(SPI_INTERNAL_RX_INT_ENABLED)

        CyIntDisable(SPI_RX_ISR_NUMBER);

        /* Set the ISR to point to the SPI_isr Interrupt. */
        (void)CyIntSetVector(SPI_RX_ISR_NUMBER, &SPI_RX_ISR);

        /* Set the priority. */
        CyIntSetPriority(SPI_RX_ISR_NUMBER, SPI_RX_ISR_PRIORITY);

    #endif /* SPI_INTERNAL_RX_INT_ENABLED */

    /* Clear any stray data from the RX and TX FIFO */
    SPI_ClearFIFO();

    #if(SPI_RX_SOFTWARE_BUF_ENABLED)
        SPI_txBufferFull = 0u;
        SPI_rxBufferRead = 0u;
        SPI_rxBufferWrite = 0u;
    #endif /* SPI_RX_SOFTWARE_BUF_ENABLED */

    #if(SPI_TX_SOFTWARE_BUF_ENABLED)
        SPI_txBufferFull = 0u;
        SPI_txBufferRead = 0u;
        SPI_txBufferWrite = 0u;
    #endif /* SPI_TX_SOFTWARE_BUF_ENABLED */

    (void) SPI_ReadTxStatus(); /* Clear any pending status bits */
    (void) SPI_ReadRxStatus(); /* Clear any pending status bits */


    /* Configure the Initial interrupt mask */
    #if (SPI_TX_SOFTWARE_BUF_ENABLED)
        SPI_TX_STATUS_MASK_REG  = (SPI_TX_INIT_INTERRUPTS_MASK &
                                                (uint8)~SPI_STS_TX_FIFO_NOT_FULL);
    #else /* SPI_TX_SOFTWARE_BUF_ENABLED */
        SPI_TX_STATUS_MASK_REG  = SPI_TX_INIT_INTERRUPTS_MASK;
    #endif /* SPI_TX_SOFTWARE_BUF_ENABLED */

    SPI_RX_STATUS_MASK_REG  = SPI_RX_INIT_INTERRUPTS_MASK;

}


/*******************************************************************************
* Function Name: SPI_Enable
********************************************************************************
*
* Summary:
*  Enable SPIS component.
*
* Parameters:
*  None.
*
* Return:
*  None.
*
*******************************************************************************/
void SPI_Enable(void) 
{
    uint8 enableInterrupts;
    enableInterrupts = CyEnterCriticalSection();

    SPI_COUNTER_CONTROL_REG |= SPI_CNTR_ENABLE;
    SPI_TX_STATUS_ACTL_REG |= SPI_INT_ENABLE;
    SPI_RX_STATUS_ACTL_REG |= SPI_INT_ENABLE;

    CyExitCriticalSection(enableInterrupts);

    #if(SPI_INTERNAL_TX_INT_ENABLED)
        CyIntEnable(SPI_TX_ISR_NUMBER);
    #endif /* SPI_INTERNAL_TX_INT_ENABLED */

    #if(SPI_INTERNAL_RX_INT_ENABLED)
        CyIntEnable(SPI_RX_ISR_NUMBER);
    #endif /* SPI_INTERNAL_RX_INT_ENABLED */
}


/*******************************************************************************
* Function Name: SPI_Start
********************************************************************************
*
* Summary:
*  Initialize and Enable the SPI Slave component.
*
* Parameters:
*  None.
*
* Return:
*  None.
*
* Global variables:
*  SPI_initVar - used to check initial configuration, modified on
*  first function call.
*
* Theory:
*  Enable the clock input to enable operation.
*
* Reentrant:
*  No.
*
*******************************************************************************/
void SPI_Start(void) 
{
    if(SPI_initVar == 0u)
    {
        SPI_Init();
        SPI_initVar = 1u;
    }

    SPI_Enable();
}


/*******************************************************************************
* Function Name: SPI_Stop
********************************************************************************
*
* Summary:
*  Disable the SPI Slave component.
*
* Parameters:
*  None.
*
* Return:
*  None.
*
* Theory:
*  Disable the internal interrupt if one is used.
*
*******************************************************************************/
void SPI_Stop(void) 
{
    uint8 enableInterrupts;
    enableInterrupts = CyEnterCriticalSection();

    SPI_TX_STATUS_ACTL_REG &= (uint8)~SPI_INT_ENABLE;
    SPI_RX_STATUS_ACTL_REG &= (uint8)~SPI_INT_ENABLE;

    CyExitCriticalSection(enableInterrupts);

    #if(SPI_INTERNAL_TX_INT_ENABLED)
        CyIntDisable(SPI_TX_ISR_NUMBER);
    #endif /* SPI_INTERNAL_TX_INT_ENABLED */

    #if(SPI_INTERNAL_RX_INT_ENABLED)
        CyIntDisable(SPI_RX_ISR_NUMBER);
    #endif /* SPI_INTERNAL_RX_INT_ENABLED */
}


/*******************************************************************************
* Function Name: SPI_EnableTxInt
********************************************************************************
*
* Summary:
*  Enable internal Tx interrupt generation.
*
* Parameters:
*  None.
*
* Return:
*  None.
*
* Theory:
*  Enable the internal Tx interrupt output -or- the interrupt component itself.
*
*******************************************************************************/
void SPI_EnableTxInt(void) 
{
    #if(SPI_INTERNAL_TX_INT_ENABLED)
        CyIntEnable(SPI_TX_ISR_NUMBER);
    #endif /* SPI_INTERNAL_TX_INT_ENABLED */
}


/*******************************************************************************
* Function Name: SPI_EnableRxInt
********************************************************************************
*
* Summary:
*  Enable internal Rx interrupt generation.
*
* Parameters:
*  None.
*
* Return:
*  None.
*
* Theory:
*  Enable the internal Rx interrupt output -or- the interrupt component itself.
*
*******************************************************************************/
void SPI_EnableRxInt(void) 
{
    #if(SPI_INTERNAL_RX_INT_ENABLED)
        CyIntEnable(SPI_RX_ISR_NUMBER);
    #endif /* SPI_INTERNAL_RX_INT_ENABLED */
}


/*******************************************************************************
* Function Name: SPI_DisableTxInt
********************************************************************************
*
* Summary:
*  Disable internal Tx interrupt generation.
*
* Parameters:
*  None.
*
* Return:
*  None.
*
* Theory:
*  Disable the internal Tx interrupt output -or- the interrupt component itself.
*
*******************************************************************************/
void SPI_DisableTxInt(void) 
{
    #if(SPI_INTERNAL_TX_INT_ENABLED)
        CyIntDisable(SPI_TX_ISR_NUMBER);
    #endif /* SPI_INTERNAL_TX_INT_ENABLED */
}


/*******************************************************************************
* Function Name: SPI_DisableRxInt
********************************************************************************
*
* Summary:
*  Disable internal Rx interrupt generation.
*
* Parameters:
*  None.
*
* Return:
*  None.
*
* Theory:
*  Disable the internal Rx interrupt output -or- the interrupt component itself.
*
*******************************************************************************/
void SPI_DisableRxInt(void) 
{
    #if(SPI_INTERNAL_RX_INT_ENABLED)
        CyIntDisable(SPI_RX_ISR_NUMBER);
    #endif /* SPI_INTERNAL_RX_INT_ENABLED */
}


/*******************************************************************************
* Function Name: SPI_SetTxInterruptMode
********************************************************************************
*
* Summary:
*  Configure which status bits trigger an interrupt event.
*
* Parameters:
*  intSrc: An or'd combination of the desired status bit masks (defined in the
*  header file).
*
* Return:
*  None.
*
* Theory:
*  Enables the output of specific status bits to the interrupt controller.
*
*******************************************************************************/
void SPI_SetTxInterruptMode(uint8 intSrc) 
{
    SPI_TX_STATUS_MASK_REG  = intSrc;
}


/*******************************************************************************
* Function Name: SPI_SetRxInterruptMode
********************************************************************************
*
* Summary:
*  Configure which status bits trigger an interrupt event.
*
* Parameters:
*  intSrc: An or'd combination of the desired status bit masks (defined in the
*  header file).
*
* Return:
*  None.
*
* Theory:
*  Enables the output of specific status bits to the interrupt controller.
*
*******************************************************************************/
void SPI_SetRxInterruptMode(uint8 intSrc) 
{
    SPI_RX_STATUS_MASK_REG  = intSrc;
}


/*******************************************************************************
* Function Name: SPI_ReadTxStatus
********************************************************************************
*
* Summary:
*  Read the Tx status register for the component.
*
* Parameters:
*  None.
*
* Return:
*  Contents of the Tx status register.
*
* Global variables:
*  SPI_swStatusTx - used to store in software status register,
*  modified every function call - resets to zero.
*
* Theory:
*  Allows the user and the API to read the Tx status register for error
*  detection and flow control.
*
* Side Effects:
*  Clear Tx status register of the component.
*
* Reentrant:
*  No.
*
*******************************************************************************/
uint8 SPI_ReadTxStatus(void) 
{
    uint8 tmpStatus;

    #if (SPI_TX_SOFTWARE_BUF_ENABLED)

        SPI_DisableTxInt();

        tmpStatus = SPI_GET_STATUS_TX(SPI_swStatusTx);

        SPI_swStatusTx = 0u;

        /* Enable Interrupts */
        SPI_EnableTxInt();

    #else /* !SPI_TX_SOFTWARE_BUF_ENABLED */

        tmpStatus = SPI_TX_STATUS_REG;

    #endif /* SPI_TX_SOFTWARE_BUF_ENABLED */

    return(tmpStatus);
}


/*******************************************************************************
* Function Name: SPI_ReadRxStatus
********************************************************************************
*
* Summary:
*  Read the Rx status register for the component.
*
* Parameters:
*  None.
*
* Return:
*  Contents of the Rx status register.
*
* Global variables:
*  SPI_swStatusRx - used to store in software Rx status register,
*  modified every function call - resets to zero.
*
* Theory:
*  Allows the user and the API to read the Rx status register for error
*  detection and flow control.
*
* Side Effects:
*  Clear Rx status register of the component.
*
* Reentrant:
*  No.
*
*******************************************************************************/
uint8 SPI_ReadRxStatus(void) 
{
    uint8 tmpStatus;

    #if (SPI_RX_SOFTWARE_BUF_ENABLED)

        SPI_DisableRxInt();

        tmpStatus = SPI_GET_STATUS_RX(SPI_swStatusRx);

        SPI_swStatusRx = 0u;

        /* Enable Interrupts */
        SPI_EnableRxInt();

    #else /* !SPI_RX_SOFTWARE_BUF_ENABLED */

        tmpStatus = SPI_RX_STATUS_REG;

    #endif /* SPI_RX_SOFTWARE_BUF_ENABLED */

    return(tmpStatus);
}


/*******************************************************************************
* Function Name: SPI_WriteTxData
********************************************************************************
*
* Summary:
*  Write a byte of data to be sent across the SPI.
*
* Parameters:
*  txDataByte: The data value to send across the SPI.
*
* Return:
*  None.
*
* Global variables:
*  SPI_txBufferWrite - used for the account of the bytes which
*  have been written down in the TX software buffer, modified every function
*  call if TX Software Buffer is used.
*  SPI_txBufferRead - used for the account of the bytes which
*  have been read from the TX software buffer.
*  SPI_txBuffer[SPI_TX_BUFFER_SIZE] - used to store
*  data to sending, modified every function call if TX Software Buffer is used.
*
* Theory:
*  Allows the user to transmit any byte of data in a single transfer.
*
* Side Effects:
*  If this function is called again before the previous byte is finished then
*  the next byte will be appended to the transfer with no time between
*  the byte transfers. Clear Tx status register of the component.
*
* Reentrant:
*  No.
*
*******************************************************************************/
void SPI_WriteTxData(uint16 txData) 
{
    #if(SPI_TX_SOFTWARE_BUF_ENABLED)

        uint8 tempStatus;
        uint8 tmpTxBufferRead;

        /* Block if buffer is full, so we don't overwrite. */
        do
        {
            tmpTxBufferRead = SPI_txBufferRead;
            if (0u == tmpTxBufferRead)
            {
                tmpTxBufferRead = SPI_TX_BUFFER_SIZE - 1u;
            }
            else
            {
                tmpTxBufferRead--;
            }

        } while(tmpTxBufferRead == SPI_txBufferWrite);

        /* Disable Interrupt to protect variables that could change on interrupt. */
        SPI_DisableTxInt();

        tempStatus = SPI_GET_STATUS_TX(SPI_swStatusTx);
        SPI_swStatusTx = tempStatus;

        if((SPI_txBufferRead == SPI_txBufferWrite) &&
            (0u != (SPI_swStatusTx & SPI_STS_TX_FIFO_NOT_FULL)))
        {
            /* Add directly to the FIFO. */
            CY_SET_REG16(SPI_TXDATA_PTR, txData);
        }
        else
        {
            /* Add to the software buffer. */
            SPI_txBufferWrite++;
            if(SPI_txBufferWrite >= SPI_TX_BUFFER_SIZE)
            {
                SPI_txBufferWrite = 0u;
            }

            if(SPI_txBufferWrite == SPI_txBufferRead)
            {
                SPI_txBufferRead++;
                if(SPI_txBufferRead >= SPI_RX_BUFFER_SIZE)
                {
                    SPI_txBufferRead = 0u;
                }
                SPI_txBufferFull = 1u;
            }

            SPI_txBuffer[SPI_txBufferWrite] = txData;

            SPI_TX_STATUS_MASK_REG |= SPI_STS_TX_FIFO_NOT_FULL;
        }

        /* Enable Interrupt. */
        SPI_EnableTxInt();

    #else /* !SPI_TX_SOFTWARE_BUF_ENABLED*/

        
        while(0u == (SPI_TX_STATUS_REG & SPI_STS_TX_FIFO_NOT_FULL))
		{
			; /* Block while FIFO is full */
		}

        /* Then write the byte */
        CY_SET_REG16(SPI_TXDATA_PTR, txData);

    #endif /* SPI_TX_SOFTWARE_BUF_ENABLED */
}

#if(SPI_MODE_USE_ZERO != 0u)

    /*******************************************************************************
    * Function Name: SPI_WriteTxDataZero
    ********************************************************************************
    *
    * Summary:
    *  Write a byte zero of data to be sent across the SPI. This must be used in
    *  Mode 00 and 01 if the FIFO is empty and data is not being sent.
    *
    * Parameters:
    *  txDataByte: The data value to send across the SPI.
    *
    * Return:
    *  None.
    *
    * Theory:
    *  Allows the user to transmit any byte of data in a single transfer. Clear
    *  status register of the component.
    *
    *******************************************************************************/
    void SPI_WriteTxDataZero(uint16 txDataByte)
                                        
    {
        CY_SET_REG16(SPI_TXDATA_ZERO_PTR, txDataByte);
    }

#endif /* (SPI_MODE_USE_ZERO != 0u) */


/*******************************************************************************
* Function Name: SPI_ReadRxData
********************************************************************************
*
* Summary:
*  Read the next byte of data received across the SPI.
*
* Parameters:
*  None.
*
* Return:
*  The next byte of data read from the FIFO.
*
* Global variables:
*  SPI_rxBufferWrite - used for the account of the bytes which
*  have been written down in the RX software buffer.
*  SPI_rxBufferRead - used for the account of the bytes which
*  have been read from the RX software buffer, modified every function
*  call if RX Software Buffer is used.
*  SPI_rxBuffer[SPI_RX_BUFFER_SIZE] - used to store
*  received data.
*
* Theory:
*  Allows the user to read a byte of data received.
*
* Side Effects:
*  Will return invalid data if the FIFO is empty.  User should poll for FIFO
*  empty status before calling Read function.
*
* Reentrant:
*  No.
*
*******************************************************************************/
uint16 SPI_ReadRxData(void) 
{
    uint16 rxData;

    #if(SPI_RX_SOFTWARE_BUF_ENABLED)

        /* Disable Interrupt to protect variables that could change on interrupt. */
        SPI_DisableRxInt();

        if(SPI_rxBufferRead != SPI_rxBufferWrite)
        {
            if(SPI_rxBufferFull == 0u)
            {
                SPI_rxBufferRead++;
                if(SPI_rxBufferRead >= SPI_RX_BUFFER_SIZE)
                {
                    SPI_rxBufferRead = 0u;
                }
            }
            else
            {
                SPI_rxBufferFull = 0u;
            }
        }

        rxData = SPI_rxBuffer[SPI_rxBufferRead];

        /* Enable Interrupt. */
        SPI_EnableRxInt();

    #else /* !SPI_RX_SOFTWARE_BUF_ENABLED */

        rxData = CY_GET_REG16(SPI_RXDATA_PTR);

    #endif /* SPI_RX_SOFTWARE_BUF_ENABLED */

    return (rxData);

}


/*******************************************************************************
* Function Name: SPI_GetRxBufferSize
********************************************************************************
*
* Summary:
*  Returns the number of bytes/words of data currently held in the RX buffer.
*  If RX Software Buffer not used then function return 0 if FIFO empty or 1 if
*  FIFO not empty. In another case function return size of RX Software Buffer.
*
* Parameters:
*  None.
*
* Return:
*  Integer count of the number of bytes/words in the RX buffer.
*
* Global variables:
*  SPI_rxBufferWrite - used for the account of the bytes which
*  have been written down in the RX software buffer.
*  SPI_rxBufferRead - used for the account of the bytes which
*  have been read from the RX software buffer.
*
* Theory:
*  Allows the user to find out how full the RX Buffer is.
*
*******************************************************************************/
uint8 SPI_GetRxBufferSize(void) 
{
    uint8 size;

    #if(SPI_RX_SOFTWARE_BUF_ENABLED)

        /* Disable Interrupt to protect variables that could change on interrupt. */
        SPI_DisableRxInt();

        if(SPI_rxBufferRead == SPI_rxBufferWrite)
        {
            size = 0u; /* No data in RX buffer */
        }
        else if(SPI_rxBufferRead < SPI_rxBufferWrite)
        {
            size = (SPI_rxBufferWrite - SPI_rxBufferRead);
        }
        else
        {
            size = (SPI_RX_BUFFER_SIZE - SPI_rxBufferRead) + SPI_rxBufferWrite;
        }

        /* Enable interrupt. */
        SPI_EnableRxInt();

    #else /* !SPI_RX_SOFTWARE_BUF_ENABLED*/

        /* We can only know if there is data in the fifo. */
        size = ((SPI_RX_STATUS_REG & SPI_STS_RX_FIFO_NOT_EMPTY) != 0u) ? 1u : 0u;

    #endif /* SPI_RX_SOFTWARE_BUF_ENABLED */

    return (size);
}


/*******************************************************************************
* Function Name: SPI_GetTxBufferSize
********************************************************************************
*
* Summary:
*  Returns the number of bytes/words of data currently held in the TX buffer.
*  If TX Software Buffer not used then function return 0 - if FIFO empty, 1 - if
*  FIFO not full, 4 - if FIFO full. In another case function return size of TX
*  Software Buffer.
*
* Parameters:
*  None.
*
* Return:
*  Integer count of the number of bytes/words in the TX buffer.
*
* Global variables:
*  SPI_txBufferWrite - used for the account of the bytes which
*  have been written down in the TX software buffer.
*  SPI_txBufferRead - used for the account of the bytes which
*  have been read from the TX software buffer.
*
* Theory:
*  Allows the user to find out how full the TX Buffer is.
*
* Side Effects:
*  Clear status register of the component.
*
*******************************************************************************/
uint8  SPI_GetTxBufferSize(void) 
{
    uint8 size;

    #if(SPI_TX_SOFTWARE_BUF_ENABLED)

        /* Disable Interrupt to protect variables that could change on interrupt. */
        SPI_DisableTxInt();

        if(SPI_txBufferRead == SPI_txBufferWrite)
        {
            size = 0u;
        }
        else if(SPI_txBufferRead < SPI_txBufferWrite)
        {
            size = (SPI_txBufferWrite - SPI_txBufferRead);
        }
        else
        {
            size = (SPI_TX_BUFFER_SIZE - SPI_txBufferRead) + SPI_txBufferWrite;
        }

        /* Enable Interrupt. */
        SPI_EnableTxInt();

    #else /* !SPI_TX_SOFTWARE_BUF_ENABLED */

        size = SPI_TX_STATUS_REG;

        /* Is the fifo is full. */
        if((size & SPI_STS_TX_FIFO_EMPTY) != 0u)
        {
            size = 0u;
        }
        else if((size & SPI_STS_TX_FIFO_NOT_FULL) != 0u)
        {
            size = 1u;
        }
        else
        {
            size = 4u;
        }

    #endif /* SPI_TX_SOFTWARE_BUF_ENABLED */

    return (size);
}


/*******************************************************************************
* Function Name: SPI_ClearRxBuffer
********************************************************************************
*
* Summary:
*  Clear the RX RAM buffer by setting the read and write pointers both to zero.
*
* Parameters:
*  None.
*
* Return:
*  None.
*
* Global variables:
*  SPI_rxBufferWrite - used for the account of the bytes which
*  have been written down in the RX software buffer, modified every function
*  call - resets to zero.
*  SPI_rxBufferRead - used for the account of the bytes which
*  have been read from the RX software buffer, modified every function call -
*  resets to zero.
*
* Theory:
*  Setting the pointers to zero makes the system believe there is no data to
*  read and writing will resume at address 0 overwriting any data that may have
*  remained in the RAM.
*
* Side Effects:
*  Any received data not read from the RAM buffer will be lost when overwritten.
*
* Reentrant:
*  No.
*
*******************************************************************************/
void SPI_ClearRxBuffer(void) 
{
    /* Clear Hardware RX FIFO */
    while((SPI_RX_STATUS_REG & SPI_STS_RX_FIFO_NOT_EMPTY) != 0u)
    {
        CY_GET_REG16(SPI_RXDATA_PTR);
    }

    #if(SPI_RX_SOFTWARE_BUF_ENABLED)

        /* Disable interrupt to protect variables that could change on interrupt. */
        SPI_DisableRxInt();

        SPI_rxBufferRead  = 0u;
        SPI_rxBufferWrite = 0u;
		SPI_rxBufferFull  = 0u;
        /* Enable interrupt. */
        SPI_EnableRxInt();

    #endif /* SPI_RX_SOFTWARE_BUF_ENABLED */
}


/*******************************************************************************
* Function Name: SPI_ClearTxBuffer
********************************************************************************
*
* Summary:
*  Clear the TX RAM buffer by setting the read and write pointers both to zero.
*
* Parameters:
*  None.
*
* Return:
*  None.
*
* Global variables:
*  SPI_txBufferWrite - used for the account of the bytes which
*  have been written down in the TX software buffer, modified every function
*  call - resets to zero.
*  SPI_txBufferRead - used for the account of the bytes which
*  have been read from the TX software buffer, modified every function call -
*  resets to zero.
*
* Theory:
*  Setting the pointers to zero makes the system believe there is no data to
*  read and writing will resume at address 0 overwriting any data that may have
*  remained in the RAM.
*
* Side Effects:
*  Any data not yet transmitted from the RAM buffer will be lost when
*  overwritten.
*
* Reentrant:
*  No.
*
*******************************************************************************/
void SPI_ClearTxBuffer(void) 
{
    uint8 enableInterrupts;

    /* Clear Hardware TX FIFO */
    enableInterrupts = CyEnterCriticalSection();

    #if(SPI_DATA_WIDTH <= 8u)

        /* Clear TX FIFO */
        SPI_TX_AUX_CONTROL_DP0_REG |= (uint8)SPI_FIFO_CLR;
        SPI_TX_AUX_CONTROL_DP0_REG &= (uint8)~SPI_FIFO_CLR;

    #else

        /* Clear TX FIFO */
        SPI_TX_AUX_CONTROL_DP0_REG |= (uint8)SPI_FIFO_CLR;
        SPI_TX_AUX_CONTROL_DP0_REG &= (uint8)~SPI_FIFO_CLR;
        SPI_TX_AUX_CONTROL_DP1_REG |= (uint8)SPI_FIFO_CLR;
        SPI_TX_AUX_CONTROL_DP1_REG &= (uint8)~SPI_FIFO_CLR;

    #endif /* SPI_DATA_WIDTH > 8u */

    CyExitCriticalSection(enableInterrupts);

    #if(SPI_TX_SOFTWARE_BUF_ENABLED)

        /* Disable Interrupt to protect variables that could change on interrupt. */
        SPI_DisableTxInt();

        SPI_txBufferRead  = 0u;
        SPI_txBufferWrite = 0u;
		SPI_txBufferFull  = 0u;
		
        /* If Buffer is empty then disable TX FIFO status interrupt */
        SPI_TX_STATUS_MASK_REG &= (uint8)~SPI_STS_TX_FIFO_NOT_FULL;

        /* Enable Interrupt. */
        SPI_EnableTxInt();

    #endif /* SPI_TX_SOFTWARE_BUF_ENABLED */
}


#if (SPI_BIDIRECTIONAL_MODE != 0u)

    /*******************************************************************************
    * Function Name: SPI_TxEnable
    ********************************************************************************
    *
    * Summary:
    *  If the SPI Slave is configured to use a single bi-directional pin then this
    *  will set the bi-directional pin to transmit.
    *
    * Parameters:
    *  None.
    *
    * Return:
    *  None.
    *
    *******************************************************************************/
    void SPI_TxEnable(void) 
    {
            SPI_CONTROL_REG |= SPI_CTRL_TX_SIGNAL_EN;
    }


    /*******************************************************************************
    * Function Name: SPI_TxDisable
    ********************************************************************************
    *
    * Summary:
    *  If the SPI Slave is configured to use a single bi-directional pin then this
    *  will set the bi-directional pin to receive.
    *
    * Parameters:
    *  None.
    *
    * Return:
    *  None.
    *
    *******************************************************************************/
    void SPI_TxDisable(void) 
    {
            SPI_CONTROL_REG &= (uint8)~SPI_CTRL_TX_SIGNAL_EN;
    }

#endif /* SPI_BIDIRECTIONAL_MODE != 0u */


/*******************************************************************************
* Function Name: SPI_PutArray
********************************************************************************
*
* Summary:
*  Write available data from RAM/ROM to the TX buffer while space is available
*  in the TX buffer. Keep trying until all data is passed to the TX buffer. If
*  used Mode 00 or 01 before PutArray() function should be called
*  WriteTxDataZero() function.
*
* Parameters:
*  *buffer: Pointer to the location in RAM containing the data to send
*  byteCount: The number of bytes to move to the transmit buffer.
*
* Return:
*  None.
*
* Side Effects:
*  Will stay in this routine until all data has been sent.  May get locked in
*  this loop if data is not being initiated by the master if there is not
*  enough room in the TX FIFO.
*
* Reentrant:
*  No.
*
*******************************************************************************/
void SPI_PutArray(const uint16 buffer[], uint8 byteCount)
                                                                    
{
    uint8 bufIndex;
    bufIndex = 0u;

    while(byteCount > 0u)
    {
        SPI_WriteTxData(buffer[bufIndex]);
        bufIndex++;
        byteCount--;
    }
}


/*******************************************************************************
* Function Name: SPI_ClearFIFO
********************************************************************************
*
* Summary:
*  Clear the RX and TX FIFO's of all data for a fresh start.
*
* Parameters:
*  None.
*
* Return:
*  None.
*
* Side Effects:
*  Clear status register of the component.
*
*******************************************************************************/
void SPI_ClearFIFO(void) 
{
    uint8 enableInterrupts;

    while((SPI_RX_STATUS_REG & SPI_STS_RX_FIFO_NOT_EMPTY) != 0u)
    {
        CY_GET_REG16(SPI_RXDATA_PTR);
    }

    enableInterrupts = CyEnterCriticalSection();

    #if(SPI_DATA_WIDTH <= 8u)

        /* Clear TX FIFO */
        SPI_TX_AUX_CONTROL_DP0_REG |= (uint8)SPI_FIFO_CLR;
        SPI_TX_AUX_CONTROL_DP0_REG &= (uint8)~SPI_FIFO_CLR;

    #else

        /* Clear TX FIFO */
        SPI_TX_AUX_CONTROL_DP0_REG |= (uint8)SPI_FIFO_CLR;
        SPI_TX_AUX_CONTROL_DP0_REG &= (uint8)~SPI_FIFO_CLR;
        SPI_TX_AUX_CONTROL_DP1_REG |= (uint8)SPI_FIFO_CLR;
        SPI_TX_AUX_CONTROL_DP1_REG &= (uint8)~SPI_FIFO_CLR;

    #endif /* SPI_DATA_WIDTH <= 8u */

    CyExitCriticalSection(enableInterrupts);
}


/* Following functions are for version Compatibility, they are obsolete.
*  Please do not use it in new projects.
*/


/*******************************************************************************
* Function Name: SPI_EnableInt
********************************************************************************
*
* Summary:
*  Enable internal interrupt generation.
*
* Parameters:
*  None.
*
* Return:
*  None.
*
* Theory:
*  Enable the internal interrupt output -or- the interrupt component itself.
*
*******************************************************************************/
void SPI_EnableInt(void) 
{
    #if(SPI_INTERNAL_TX_INT_ENABLED)
        CyIntEnable(SPI_TX_ISR_NUMBER);
    #endif /* SPI_INTERNAL_TX_INT_ENABLED */

    #if(SPI_INTERNAL_RX_INT_ENABLED)
        CyIntEnable(SPI_RX_ISR_NUMBER);
    #endif /* SPI_INTERNAL_RX_INT_ENABLED */
}


/*******************************************************************************
* Function Name: SPI_DisableInt
********************************************************************************
*
* Summary:
*  Disable internal interrupt generation.
*
* Parameters:
*  None.
*
* Return:
*  None.
*
* Theory:
*  Disable the internal interrupt output -or- the interrupt component itself.
*
*******************************************************************************/
void SPI_DisableInt(void) 
{
    #if(SPI_INTERNAL_TX_INT_ENABLED)
        CyIntDisable(SPI_TX_ISR_NUMBER);
    #endif /* SPI_INTERNAL_TX_INT_ENABLED */

    #if(SPI_INTERNAL_RX_INT_ENABLED)
        CyIntDisable(SPI_RX_ISR_NUMBER);
    #endif /* SPI_INTERNAL_RX_INT_ENABLED */
}


/*******************************************************************************
* Function Name: SPI_SetInterruptMode
********************************************************************************
*
* Summary:
*  Configure which status bits trigger an interrupt event.
*
* Parameters:
*  intSrc: An or'd combination of the desired status bit masks (defined in the
*  header file).
*
* Return:
*  None.
*
* Theory:
*  Enables the output of specific status bits to the interrupt controller.
*
*******************************************************************************/
void SPI_SetInterruptMode(uint8 intSrc) 
{
    SPI_TX_STATUS_MASK_REG  = intSrc;
    SPI_RX_STATUS_MASK_REG  = intSrc;
}


/*******************************************************************************
* Function Name: SPI_ReadStatus
********************************************************************************
*
* Summary:
*  Read the status register for the component.
*
* Parameters:
*  None.
*
* Return:
*  Contents of the status register.
*
* Global variables:
*  SPI_swStatus - used to store in software status register,
*  modified every function call - resets to zero.
*
* Theory:
*  Allows the user and the API to read the status register for error detection
*  and flow control.
*
* Side Effects:
*  Clear status register of the component.
*
* Reentrant:
*  No.
*
*******************************************************************************/
uint8 SPI_ReadStatus(void) 
{
    uint8 tmpStatus;

    #if ((SPI_TX_SOFTWARE_BUF_ENABLED) || (SPI_RX_SOFTWARE_BUF_ENABLED))

        SPI_DisableInt();

        tmpStatus = SPI_GET_STATUS_TX(SPI_swStatusTx) |
              (SPI_GET_STATUS_RX(SPI_swStatusRx) & (uint8)~SPI_STS_RX_FIFO_FULL);

        SPI_swStatusTx = 0u;
        SPI_swStatusRx = 0u;

        /* Enable Interrupts */
        SPI_EnableInt();

    #else /* !((SPI_TX_SOFTWARE_BUF_ENABLED) || (SPI_RX_SOFTWARE_BUF_ENABLED)) */

        tmpStatus = SPI_TX_STATUS_REG | (SPI_RX_STATUS_REG &
                                                      (uint8)~SPI_STS_RX_FIFO_FULL);

    #endif /* (SPI_TX_SOFTWARE_BUF_ENABLED) || (SPI_RX_SOFTWARE_BUF_ENABLED) */

    return(tmpStatus);
}


/* [] END OF FILE */
