trehansiddharth/SignAway/Source/PSoC/SignatureVerifier/SignatureVerifier.cydsn/codegentemp/SPI_Clock.h

/*******************************************************************************
* File Name: SPI_Clock.h
* Version 2.20
*
*  Description:
*   Provides the function and constant definitions for the clock component.
*
*  Note:
*
********************************************************************************
* Copyright 2008-2012, Cypress Semiconductor Corporation.  All rights reserved.
* You may use this file only in accordance with the license, terms, conditions, 
* disclaimers, and limitations in the end user license agreement accompanying 
* the software package with which this file was provided.
*******************************************************************************/

#if !defined(CY_CLOCK_SPI_Clock_H)
#define CY_CLOCK_SPI_Clock_H

#include <cytypes.h>
#include <cyfitter.h>


/***************************************
*        Function Prototypes
***************************************/
#if defined CYREG_PERI_DIV_CMD

void SPI_Clock_StartEx(uint32 alignClkDiv);
#define SPI_Clock_Start() \
    SPI_Clock_StartEx(SPI_Clock__PA_DIV_ID)

#else

void SPI_Clock_Start(void);

#endif/* CYREG_PERI_DIV_CMD */

void SPI_Clock_Stop(void);

void SPI_Clock_SetFractionalDividerRegister(uint16 clkDivider, uint8 clkFractional);

uint16 SPI_Clock_GetDividerRegister(void);
uint8  SPI_Clock_GetFractionalDividerRegister(void);

#define SPI_Clock_Enable()                         SPI_Clock_Start()
#define SPI_Clock_Disable()                        SPI_Clock_Stop()
#define SPI_Clock_SetDividerRegister(clkDivider, reset)  \
    SPI_Clock_SetFractionalDividerRegister((clkDivider), 0u)
#define SPI_Clock_SetDivider(clkDivider)           SPI_Clock_SetDividerRegister((clkDivider), 1u)
#define SPI_Clock_SetDividerValue(clkDivider)      SPI_Clock_SetDividerRegister((clkDivider) - 1u, 1u)


/***************************************
*             Registers
***************************************/
#if defined CYREG_PERI_DIV_CMD

#define SPI_Clock_DIV_ID     SPI_Clock__DIV_ID

#define SPI_Clock_CMD_REG    (*(reg32 *)CYREG_PERI_DIV_CMD)
#define SPI_Clock_CTRL_REG   (*(reg32 *)SPI_Clock__CTRL_REGISTER)
#define SPI_Clock_DIV_REG    (*(reg32 *)SPI_Clock__DIV_REGISTER)

#define SPI_Clock_CMD_DIV_SHIFT          (0u)
#define SPI_Clock_CMD_PA_DIV_SHIFT       (8u)
#define SPI_Clock_CMD_DISABLE_SHIFT      (30u)
#define SPI_Clock_CMD_ENABLE_SHIFT       (31u)

#define SPI_Clock_CMD_DISABLE_MASK       ((uint32)((uint32)1u << SPI_Clock_CMD_DISABLE_SHIFT))
#define SPI_Clock_CMD_ENABLE_MASK        ((uint32)((uint32)1u << SPI_Clock_CMD_ENABLE_SHIFT))

#define SPI_Clock_DIV_FRAC_MASK  (0x000000F8u)
#define SPI_Clock_DIV_FRAC_SHIFT (3u)
#define SPI_Clock_DIV_INT_MASK   (0xFFFFFF00u)
#define SPI_Clock_DIV_INT_SHIFT  (8u)

#else 

#define SPI_Clock_DIV_REG        (*(reg32 *)SPI_Clock__REGISTER)
#define SPI_Clock_ENABLE_REG     SPI_Clock_DIV_REG
#define SPI_Clock_DIV_FRAC_MASK  SPI_Clock__FRAC_MASK
#define SPI_Clock_DIV_FRAC_SHIFT (16u)
#define SPI_Clock_DIV_INT_MASK   SPI_Clock__DIVIDER_MASK
#define SPI_Clock_DIV_INT_SHIFT  (0u)

#endif/* CYREG_PERI_DIV_CMD */

#endif /* !defined(CY_CLOCK_SPI_Clock_H) */

/* [] END OF FILE */
