trehansiddharth/SignAway/Source/PSoC/SignatureVerifier/SignatureVerifier.cydsn/codegentemp/UART_PM.c

/*******************************************************************************
* File Name: UART_PM.c
* Version 1.20
*
* Description:
*  This file provides the source code to the Power Management support for
*  the SCB Component.
*
* Note:
*
********************************************************************************
* Copyright 2013-2014, Cypress Semiconductor Corporation.  All rights reserved.
* You may use this file only in accordance with the license, terms, conditions,
* disclaimers, and limitations in the end user license agreement accompanying
* the software package with which this file was provided.
*******************************************************************************/

#include "UART.h"
#include "UART_PVT.h"

#if(UART_SCB_MODE_I2C_INC)
    #include "UART_I2C_PVT.h"
#endif /* (UART_SCB_MODE_I2C_INC) */

#if(UART_SCB_MODE_EZI2C_INC)
    #include "UART_EZI2C_PVT.h"
#endif /* (UART_SCB_MODE_EZI2C_INC) */

#if(UART_SCB_MODE_SPI_INC || UART_SCB_MODE_UART_INC)
    #include "UART_SPI_UART_PVT.h"
#endif /* (UART_SCB_MODE_SPI_INC || UART_SCB_MODE_UART_INC) */


/***************************************
*   Backup Structure declaration
***************************************/

#if(UART_SCB_MODE_UNCONFIG_CONST_CFG || \
   (UART_SCB_MODE_I2C_CONST_CFG   && (!UART_I2C_WAKE_ENABLE_CONST))   || \
   (UART_SCB_MODE_EZI2C_CONST_CFG && (!UART_EZI2C_WAKE_ENABLE_CONST)) || \
   (UART_SCB_MODE_SPI_CONST_CFG   && (!UART_SPI_WAKE_ENABLE_CONST))   || \
   (UART_SCB_MODE_UART_CONST_CFG  && (!UART_UART_WAKE_ENABLE_CONST)))

    UART_BACKUP_STRUCT UART_backup =
    {
        0u, /* enableState */
    };
#endif


/*******************************************************************************
* Function Name: UART_Sleep
********************************************************************************
*
* Summary:
*  Prepares the component to enter Deep Sleep.
*  The “Enable wakeup from Sleep Mode” selection has an influence on
*  this function implementation.
*
* Parameters:
*  None
*
* Return:
*  None
*
*******************************************************************************/
void UART_Sleep(void)
{
#if(UART_SCB_MODE_UNCONFIG_CONST_CFG)

    if(UART_SCB_WAKE_ENABLE_CHECK)
    {
        if(UART_SCB_MODE_I2C_RUNTM_CFG)
        {
            UART_I2CSaveConfig();
        }
        else if(UART_SCB_MODE_EZI2C_RUNTM_CFG)
        {
            UART_EzI2CSaveConfig();
        }
    #if(!UART_CY_SCBIP_V1_I2C_ONLY)
        else if(UART_SCB_MODE_SPI_RUNTM_CFG)
        {
            UART_SpiSaveConfig();
        }
        else if(UART_SCB_MODE_UART_RUNTM_CFG)
        {
            UART_UartSaveConfig();
        }
    #endif /* (!UART_CY_SCBIP_V1_I2C_ONLY) */
        else
        {
            /* Unknown mode: do nothing */
        }
    }
    else
    {
        UART_backup.enableState = (uint8) UART_GET_CTRL_ENABLED;

        if(0u != UART_backup.enableState)
        {
            UART_Stop();
        }
    }

#else

    #if (UART_SCB_MODE_I2C_CONST_CFG && UART_I2C_WAKE_ENABLE_CONST)
        UART_I2CSaveConfig();

    #elif (UART_SCB_MODE_EZI2C_CONST_CFG && UART_EZI2C_WAKE_ENABLE_CONST)
        UART_EzI2CSaveConfig();

    #elif (UART_SCB_MODE_SPI_CONST_CFG && UART_SPI_WAKE_ENABLE_CONST)
        UART_SpiSaveConfig();

    #elif (UART_SCB_MODE_UART_CONST_CFG && UART_UART_WAKE_ENABLE_CONST)
        UART_UartSaveConfig();

    #else

        UART_backup.enableState = (uint8) UART_GET_CTRL_ENABLED;

        if(0u != UART_backup.enableState)
        {
            UART_Stop();
        }

    #endif /* defined (UART_SCB_MODE_I2C_CONST_CFG) && (UART_I2C_WAKE_ENABLE_CONST) */

#endif /* (UART_SCB_MODE_UNCONFIG_CONST_CFG) */
}


/*******************************************************************************
* Function Name: UART_Wakeup
********************************************************************************
*
* Summary:
*  Prepares the component for the Active mode operation after exiting Deep Sleep.
*  The “Enable wakeup from Sleep Mode” option has an influence on this function
*  implementation.
*  This function should not be called after exiting Sleep.
*
* Parameters:
*  None
*
* Return:
*  None
*
*******************************************************************************/
void UART_Wakeup(void)
{
#if(UART_SCB_MODE_UNCONFIG_CONST_CFG)

    if(UART_SCB_WAKE_ENABLE_CHECK)
    {
        if(UART_SCB_MODE_I2C_RUNTM_CFG)
        {
            UART_I2CRestoreConfig();
        }
        else if(UART_SCB_MODE_EZI2C_RUNTM_CFG)
        {
            UART_EzI2CRestoreConfig();
        }
    #if(!UART_CY_SCBIP_V1_I2C_ONLY)
        else if(UART_SCB_MODE_SPI_RUNTM_CFG)
        {
            UART_SpiRestoreConfig();
        }
        else if(UART_SCB_MODE_UART_RUNTM_CFG)
        {
            UART_UartRestoreConfig();
        }
    #endif /* (!UART_CY_SCBIP_V1_I2C_ONLY) */
        else
        {
            /* Unknown mode: do nothing */
        }
    }
    else
    {
        if(0u != UART_backup.enableState)
        {
            UART_Enable();
        }
    }

#else

    #if (UART_SCB_MODE_I2C_CONST_CFG  && UART_I2C_WAKE_ENABLE_CONST)
        UART_I2CRestoreConfig();

    #elif (UART_SCB_MODE_EZI2C_CONST_CFG && UART_EZI2C_WAKE_ENABLE_CONST)
        UART_EzI2CRestoreConfig();

    #elif (UART_SCB_MODE_SPI_CONST_CFG && UART_SPI_WAKE_ENABLE_CONST)
        UART_SpiRestoreConfig();

    #elif (UART_SCB_MODE_UART_CONST_CFG && UART_UART_WAKE_ENABLE_CONST)
        UART_UartRestoreConfig();

    #else

        if(0u != UART_backup.enableState)
        {
            UART_Enable();
        }

    #endif /* (UART_I2C_WAKE_ENABLE_CONST) */

#endif /* (UART_SCB_MODE_UNCONFIG_CONST_CFG) */
}


/* [] END OF FILE */
