trehansiddharth/SignAway/Source/PSoC/SignatureVerifier/SignatureVerifier.cydsn/codegentemp/SPI_PM.c

/*******************************************************************************
* File Name: SPI_PM.c
* Version 2.60
*
* Description:
*  This file contains the setup, control and status commands to support
*  component operations in low power mode.
*
* Note:
*
********************************************************************************
* Copyright 2008-2013, Cypress Semiconductor Corporation.  All rights reserved.
* You may use this file only in accordance with the license, terms, conditions,
* disclaimers, and limitations in the end user license agreement accompanying
* the software package with which this file was provided.
*******************************************************************************/

#include "SPI_PVT.h"

static SPI_BACKUP_STRUCT SPI_backup = 
{
    SPI_DISABLED,
    SPI_BITCTR_INIT,
    #if(CY_UDB_V0)
        SPI_TX_INIT_INTERRUPTS_MASK,
        SPI_RX_INIT_INTERRUPTS_MASK
    #endif /* CY_UDB_V0 */
};


/*******************************************************************************
* Function Name: SPI_SaveConfig
********************************************************************************
*
* Summary:
*  Saves SPIM configuration.
*
* Parameters:
*  None.
*
* Return:
*  None.
*
* Global Variables:
*  SPI_backup - modified when non-retention registers are saved.
*
* Reentrant:
*  No.
*
*******************************************************************************/
void SPI_SaveConfig(void) 
{
    /* Store Status Mask registers */
    #if (CY_UDB_V0)

       SPI_backup.saveSrTxIntMask = SPI_TX_STATUS_MASK_REG;
       SPI_backup.saveSrRxIntMask = SPI_RX_STATUS_MASK_REG;
       SPI_backup.cntrPeriod      = SPI_COUNTER_PERIOD_REG;

    #endif /* CY_UDB_V0 */
}


/*******************************************************************************
* Function Name: SPI_RestoreConfig
********************************************************************************
*
* Summary:
*  Restores SPIS configuration.
*
* Parameters:
*  None.
*
* Return:
*  None.
*
* Global Variables:
*  SPI_backup - used when non-retention registers are restored.
*
* Side Effects:
*  If this API is called without first calling SaveConfig then in the following
*  registers will be default values from Customizer:
*  SPI_STATUS_MASK_REG and SPI_COUNTER_PERIOD_REG.
*
*******************************************************************************/
void SPI_RestoreConfig(void) 
{
    /* Restore the data, saved by SaveConfig() function */
    #if (CY_UDB_V0)

        SPI_TX_STATUS_MASK_REG = SPI_backup.saveSrTxIntMask;
        SPI_RX_STATUS_MASK_REG = SPI_backup.saveSrRxIntMask;
        SPI_COUNTER_PERIOD_REG = SPI_backup.cntrPeriod;

    #endif /* CY_UDB_V0 */
}


/*******************************************************************************
* Function Name: SPI_Sleep
********************************************************************************
*
* Summary:
*  Prepare SPIM Component goes to sleep.
*
* Parameters:
*  None.
*
* Return:
*  None.
*
* Global Variables:
*  SPI_backup - modified when non-retention registers are saved.
*
* Reentrant:
*  No.
*
*******************************************************************************/
void SPI_Sleep(void) 
{
    /* Save components enable state */
    if ((SPI_TX_STATUS_ACTL_REG & SPI_INT_ENABLE) != 0u)
    {
        SPI_backup.enableState = 1u;
    }
    else /* Components block is disabled */
    {
        SPI_backup.enableState = 0u;
    }

    SPI_Stop();

    SPI_SaveConfig();
}


/*******************************************************************************
* Function Name: SPI_Wakeup
********************************************************************************
*
* Summary:
*  Prepare SPIM Component to wake up.
*
* Parameters:
*  None.
*
* Return:
*  None.
*
* Global Variables:
*  SPI_backup - used when non-retention registers are restored.
*  SPI_txBufferWrite - modified every function call - resets to
*  zero.
*  SPI_txBufferRead - modified every function call - resets to
*  zero.
*  SPI_rxBufferWrite - modified every function call - resets to
*  zero.
*  SPI_rxBufferRead - modified every function call - resets to
*  zero.
*
* Reentrant:
*  No.
*
*******************************************************************************/
void SPI_Wakeup(void) 
{
    SPI_RestoreConfig();

    #if (SPI_TX_SOFTWARE_BUF_ENABLED)
        SPI_txBufferFull = 0u;
        SPI_txBufferRead = 0u;
        SPI_txBufferWrite = 0u;
    #endif /* SPI_TX_SOFTWARE_BUF_ENABLED */

    #if (SPI_RX_SOFTWARE_BUF_ENABLED)
        SPI_rxBufferFull = 0u;
        SPI_rxBufferRead = 0u;
        SPI_rxBufferWrite = 0u;
    #endif /* SPI_RX_SOFTWARE_BUF_ENABLED */

    SPI_ClearFIFO();

    /* Restore components block enable state */
    if (SPI_backup.enableState != 0u)
    {
         /* Components block was enabled */
         SPI_Enable();
    } /* Do nothing if components block was disabled */
}


/* [] END OF FILE */
