trehansiddharth/SignAway/Source/PSoC/SignatureVerifier/SignatureVerifier.cydsn/codegentemp/isr_spi.h

/*******************************************************************************
* File Name: isr_spi.h
* Version 1.70
*
*  Description:
*   Provides the function definitions for the Interrupt Controller.
*
*
********************************************************************************
* Copyright 2008-2012, Cypress Semiconductor Corporation.  All rights reserved.
* You may use this file only in accordance with the license, terms, conditions, 
* disclaimers, and limitations in the end user license agreement accompanying 
* the software package with which this file was provided.
*******************************************************************************/
#if !defined(CY_ISR_isr_spi_H)
#define CY_ISR_isr_spi_H


#include <cytypes.h>
#include <cyfitter.h>

/* Interrupt Controller API. */
void isr_spi_Start(void);
void isr_spi_StartEx(cyisraddress address);
void isr_spi_Stop(void);

CY_ISR_PROTO(isr_spi_Interrupt);

void isr_spi_SetVector(cyisraddress address);
cyisraddress isr_spi_GetVector(void);

void isr_spi_SetPriority(uint8 priority);
uint8 isr_spi_GetPriority(void);

void isr_spi_Enable(void);
uint8 isr_spi_GetState(void);
void isr_spi_Disable(void);

void isr_spi_SetPending(void);
void isr_spi_ClearPending(void);


/* Interrupt Controller Constants */

/* Address of the INTC.VECT[x] register that contains the Address of the isr_spi ISR. */
#define isr_spi_INTC_VECTOR            ((reg32 *) isr_spi__INTC_VECT)

/* Address of the isr_spi ISR priority. */
#define isr_spi_INTC_PRIOR             ((reg32 *) isr_spi__INTC_PRIOR_REG)

/* Priority of the isr_spi interrupt. */
#define isr_spi_INTC_PRIOR_NUMBER      isr_spi__INTC_PRIOR_NUM

/* Address of the INTC.SET_EN[x] byte to bit enable isr_spi interrupt. */
#define isr_spi_INTC_SET_EN            ((reg32 *) isr_spi__INTC_SET_EN_REG)

/* Address of the INTC.CLR_EN[x] register to bit clear the isr_spi interrupt. */
#define isr_spi_INTC_CLR_EN            ((reg32 *) isr_spi__INTC_CLR_EN_REG)

/* Address of the INTC.SET_PD[x] register to set the isr_spi interrupt state to pending. */
#define isr_spi_INTC_SET_PD            ((reg32 *) isr_spi__INTC_SET_PD_REG)

/* Address of the INTC.CLR_PD[x] register to clear the isr_spi interrupt. */
#define isr_spi_INTC_CLR_PD            ((reg32 *) isr_spi__INTC_CLR_PD_REG)



#endif /* CY_ISR_isr_spi_H */


/* [] END OF FILE */
