trehansiddharth/SignAway/Source/PSoC/SignatureVerifier/SignatureVerifier.cydsn/codegentemp/SPI_PVT.h

/*******************************************************************************
* File Name: .h
* Version 2.60
*
* Description:
*  This private header file contains internal definitions for the SPIS
*  component. Do not use these definitions directly in your application.
*
* Note:
*
********************************************************************************
* Copyright 2013, Cypress Semiconductor Corporation. All rights reserved.
* You may use this file only in accordance with the license, terms, conditions,
* disclaimers, and limitations in the end user license agreement accompanying
* the software package with which this file was provided.
*******************************************************************************/

#if !defined(CY_SPIS_PVT_SPI_H)
#define CY_SPIS_PVT_SPI_H

#include "SPI.h"


/**********************************
*   Functions with external linkage
**********************************/


/**********************************
*   Variables with external linkage
**********************************/
extern volatile uint8 SPI_swStatusTx;
extern volatile uint8 SPI_swStatusRx;

#if (SPI_RX_SOFTWARE_BUF_ENABLED)

    extern volatile uint16 SPI_rxBuffer[SPI_RX_BUFFER_SIZE];
    extern volatile uint8 SPI_rxBufferRead;
    extern volatile uint8 SPI_rxBufferWrite;
    extern volatile uint8 SPI_rxBufferFull;

#endif /* SPI_RX_SOFTWARE_BUF_ENABLED */

#if (SPI_TX_SOFTWARE_BUF_ENABLED)

    extern volatile uint16 SPI_txBuffer[SPI_TX_BUFFER_SIZE];
    extern volatile uint8 SPI_txBufferRead;
    extern volatile uint8 SPI_txBufferWrite;
    extern volatile uint8 SPI_txBufferFull;

#endif /* SPI_TX_SOFTWARE_BUF_ENABLED */

#endif /* CY_SPIS_PVT_SPI_H */


/* [] END OF FILE */
